schizobovine/uvdosimeter/hardware/uv-dosimeter-featherwing-mk-2.0.brd

## EAGLE design hardware/uv-dosimeter-featherwing-mk-2.0.brd (2016-05-01)

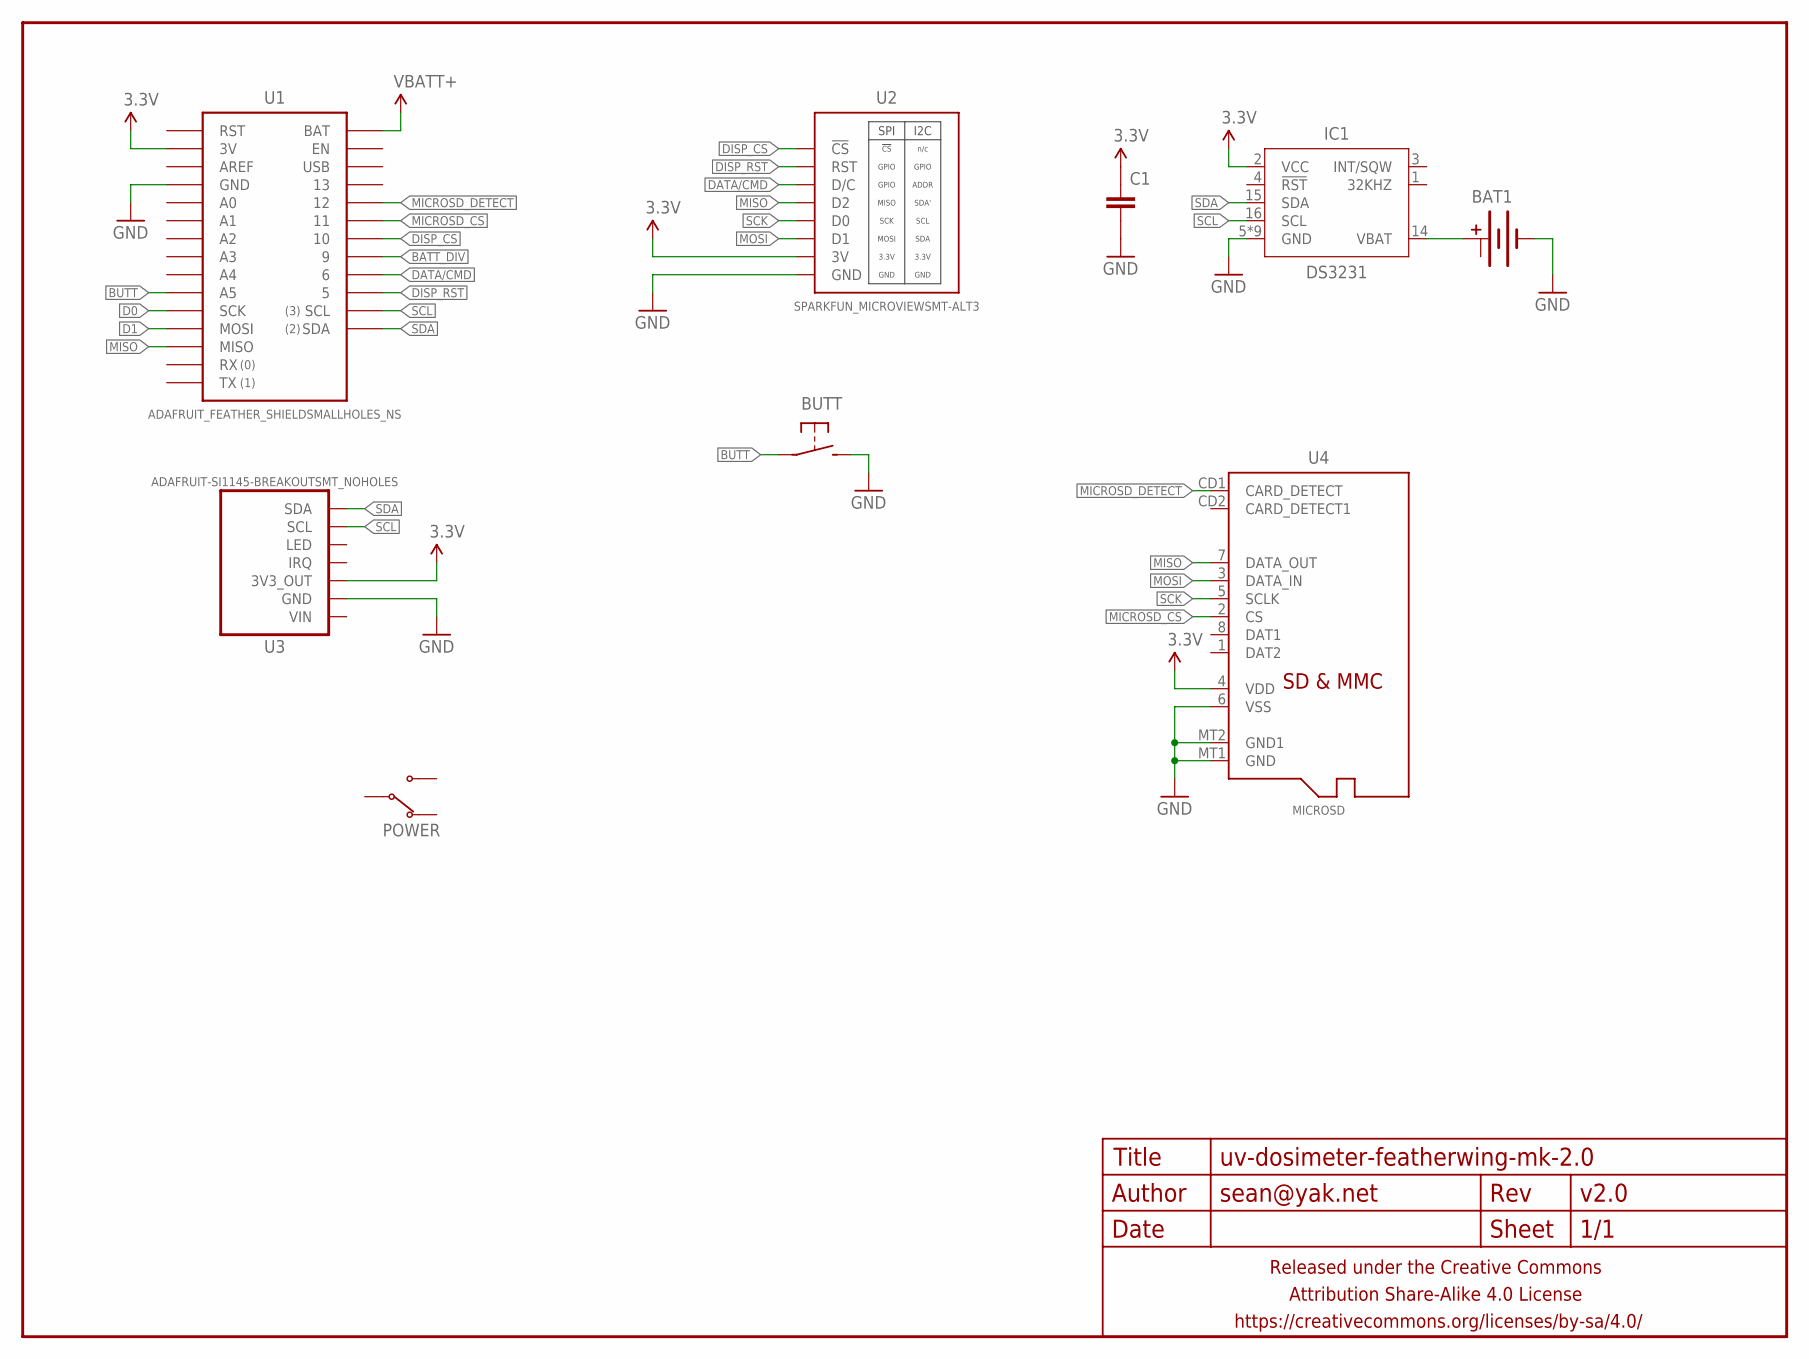
[picture p20: schematic uv-dosimeter-featherwing-mk-2.0.sch]

Parts:
BAT1: BATTERY-COINCR1225_SMD_SMALLER; BATTCON_12MM_SMD
BUTT: SPST-NO-TACT3MM-SMD; DTSM-3
C1: CAPACITOR-CERAMICC0603; C0603
FRAME1: FRAME-LETTERNO_PACKAGE; DUMMY
IC1: DS3231; SO16W
POWER: SWITCH-SPDTSMD-RA; SWITCH-SPDT-SMD-RA
U1: ADAFRUIT_FEATHER_SHIELDSMALLHOLES_NS; ADAFRUIT_FEATHER_SMALLHOLES_NS
U2: SPARKFUN_MICROVIEWSMT-ALT3; SPARKFUN-MICROVIEW-SMT-ALT3
U3: ADAFRUIT-SI1145-BREAKOUTSMT_NOHOLES; ADAFRUIT-SI1145-BREAKOUT-SMT-NOHOLES
U4: MICROSD

Connections:
3.3V: C1.1, IC1.2 (VCC), U1.3V, U2.3V, U3.3V3 (3V3_OUT)
BATT_DIV: U1.9
BUTT: BUTT.1, U1.A5
D0: U1.SCK
D1: U1.MOSI
DATA/CMD: U1.6, U2.D/C
DISP_CS: U1.10, U2.CS (!CS)
DISP_RST: U1.5, U2.RST
GND: BAT1.-, BUTT.2, C1.2, IC1.5 (GND), IC1.6 (GND), IC1.7 (GND), IC1.8 (GND), IC1.9 (GND), IC1.10 (GND), IC1.11 (GND), IC1.12 (GND), IC1.13 (GND), U1.GND@0 (GND), U1.GND@1 (GND), U2.GND, U3.GND, U4.6 (VSS), U4.MT1 (GND)
MICROSD_CS: U1.11, U4.2 (CS)
MICROSD_DETECT: U1.12, U4.CD1 (CARD_DETECT)
MISO: U1.MISO, U2.D2, U4.7 (DATA_OUT)
MOSI: U2.D1, U4.3 (DATA_IN)
unnamed: BAT1.+@1 (+), IC1.14 (VBAT)
SCK: U2.D0, U4.5 (SCLK)
SCL: IC1.16 (SCL), U1.SCL, U3.SCL
SDA: IC1.15 (SDA), U1.SDA, U3.SDA
VBATT+: U1.BAT
VDD: U4.4 (VDD)

Board: 2 copper layers, 12 parts (7 on the bottom side), 14 nets, no tracks yet.

Other parts of the board:
U$1: COW_SMALL
U$5: CC-BY-SA-4.0-NO-URL
