schizobovine/uvdosimeter/hardware/uv-dosimeter-featherwing-mk-1.3.brd

## EAGLE design hardware/uv-dosimeter-featherwing-mk-1.3.brd (2016-05-01)

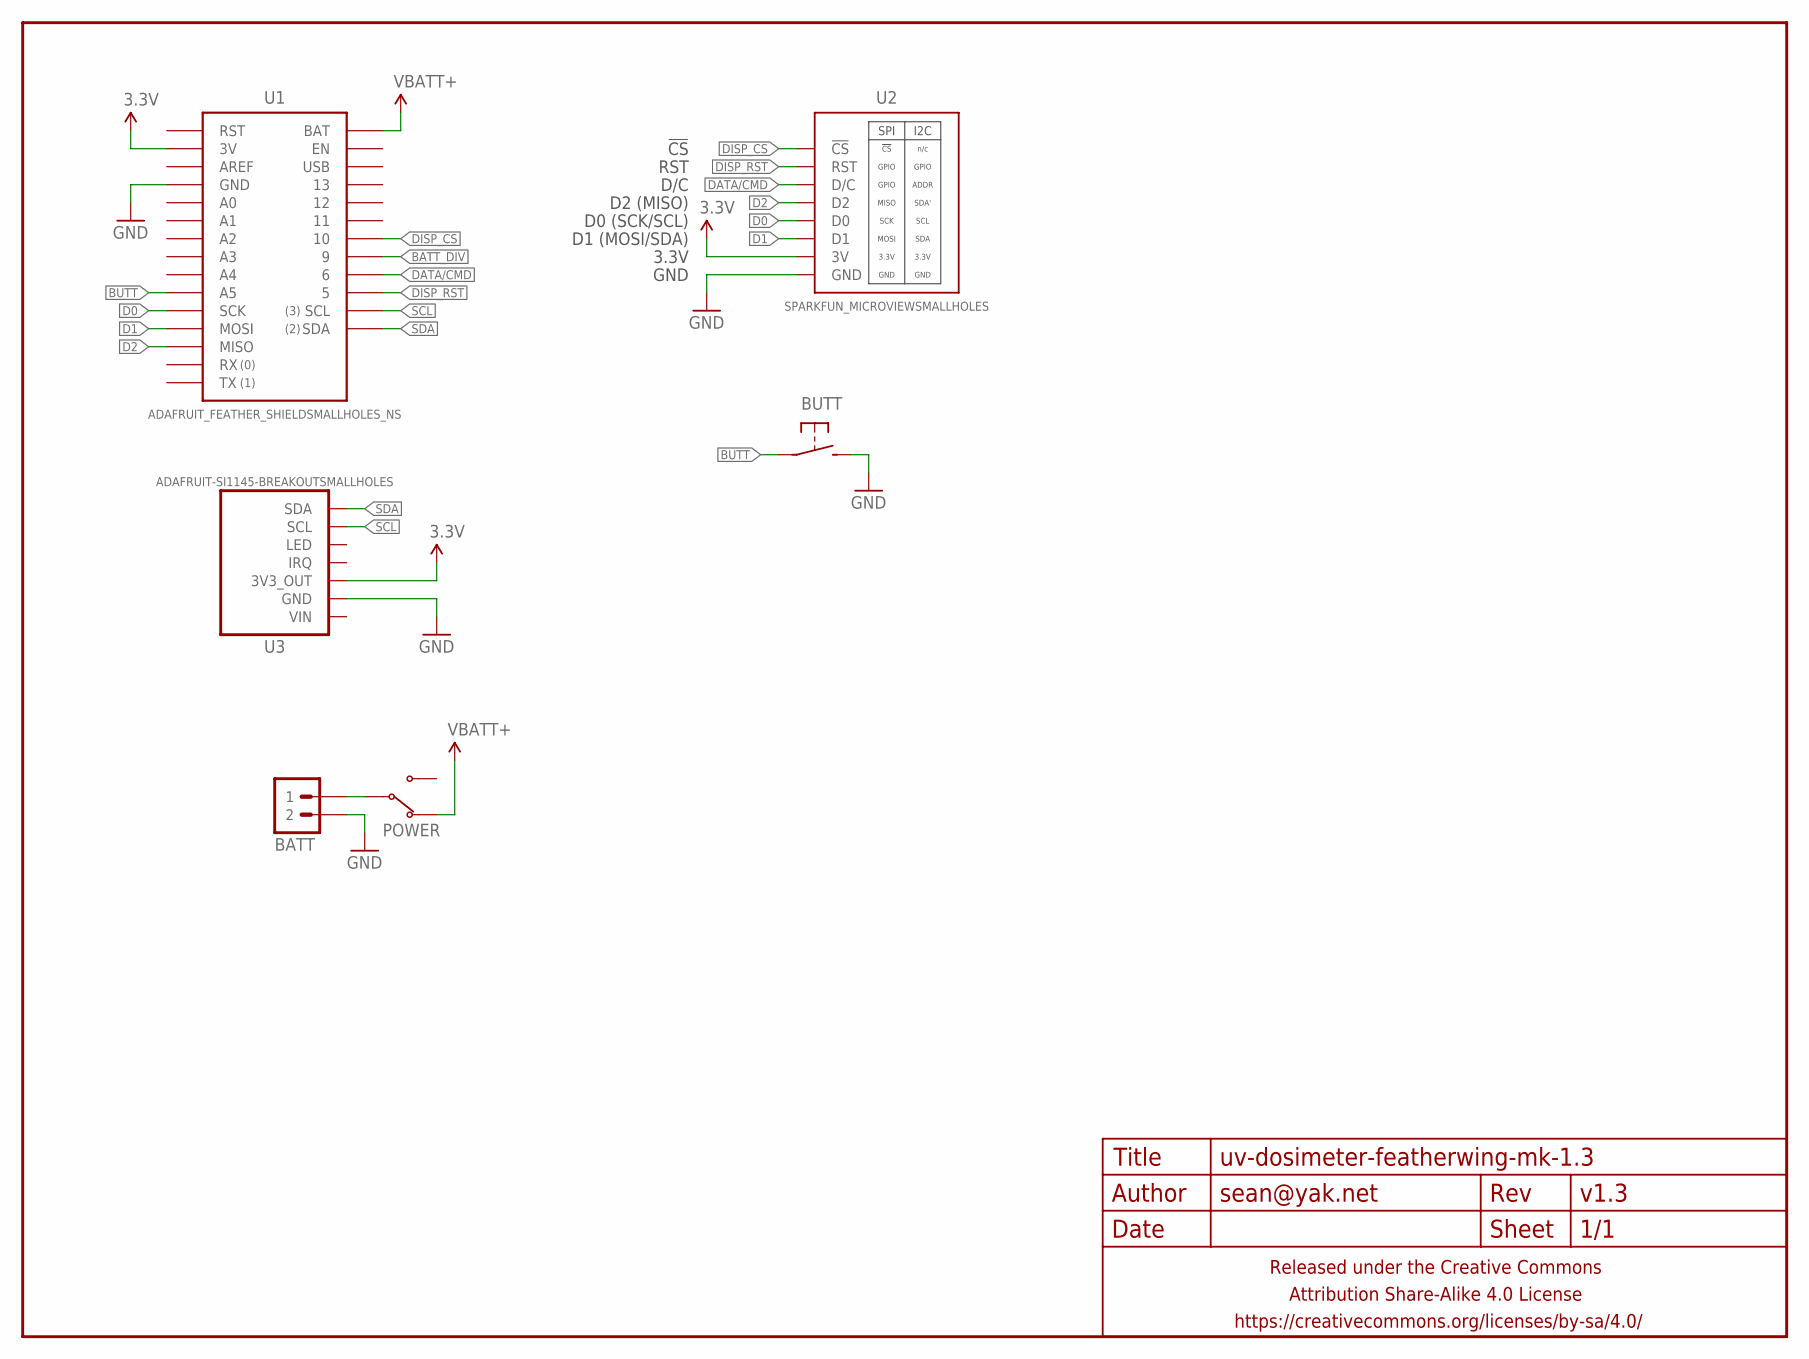
[picture p21: schematic uv-dosimeter-featherwing-mk-1.3.sch]

Parts:
BATT: M02JST-2MM-SMT; JST-2-SMD
BUTT: SPST-NO-TACT3MM-PTH-SMALL-PADS; DTS-3-SMALL-PADS
FRAME1: FRAME-LETTERNO_PACKAGE; DUMMY
POWER: SWITCH-SPDTPTH-VERT-2.54MM; SWITCH-SPDT
U1: ADAFRUIT_FEATHER_SHIELDSMALLHOLES_NS; ADAFRUIT_FEATHER_SMALLHOLES_NS
U2: SPARKFUN_MICROVIEWSMALLHOLES; SPARKFUN-MICROVIEW-SMALLHOLES
U3: ADAFRUIT-SI1145-BREAKOUTSMALLHOLES; ADAFRUIT-SI1145-BREAKOUT-LESSSILK-SMALLHOLES

Connections:
3.3V: U1.3V, U2.3V, U3.3V3_OUT
BATT_DIV: U1.9
BUTT: BUTT.1, U1.A5
D0: U1.SCK, U2.D0
D1: U1.MOSI, U2.D1
D2: U1.MISO, U2.D2
DATA/CMD: U1.6, U2.D/C
DISP_CS: U1.10, U2.CS (!CS)
DISP_RST: U1.5, U2.RST
GND: BATT.1 (2), BUTT.2, U1.GND@0 (GND), U1.GND@1 (GND), U2.GND, U3.GND
unnamed: BATT.2 (1), POWER.2 (COM)
SCL: U1.SCL, U3.SCL
SDA: U1.SDA, U3.SDA
VBATT+: POWER.1 (NC), U1.BAT

Notes on the sheet:
GND
3.3V
D1 (MOSI/SDA)
D0 (SCK/SCL)
D2 (MISO)
D/C
RST
!CS

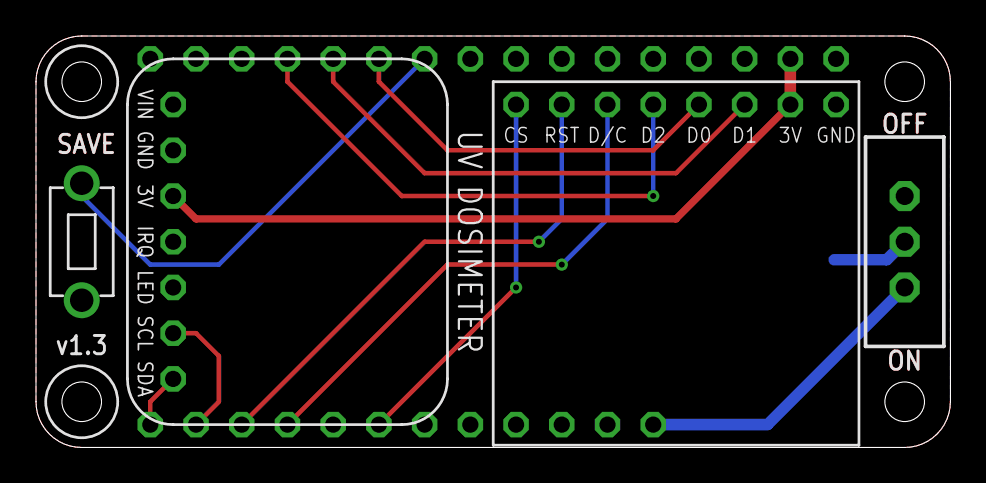
[picture p22: board uv-dosimeter-featherwing-mk-1.3.brd from above]

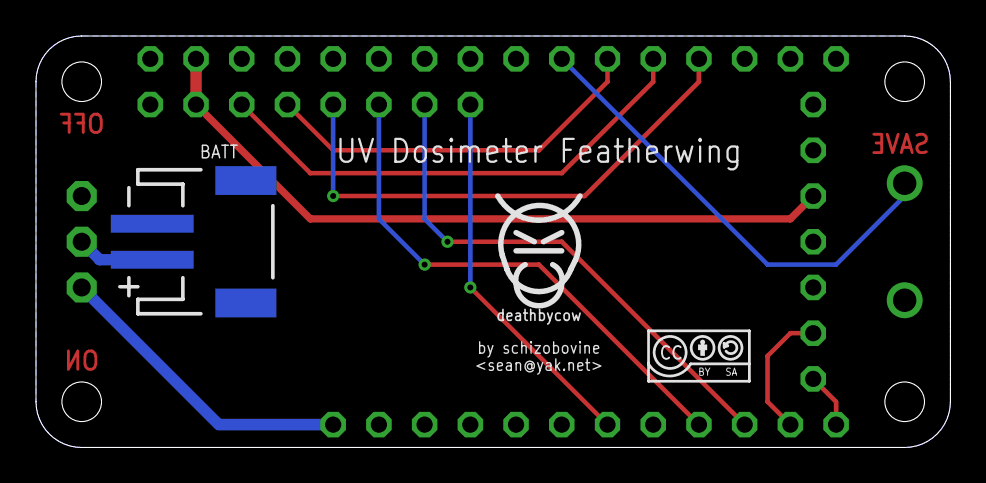
[picture p23: board uv-dosimeter-featherwing-mk-1.3.brd from below]

Board: 2 copper layers, 50.8 x 22.9 mm, 9 parts (4 on the bottom side), 13 nets.

Other parts of the board:
U$1: COW_SMALL
U$5: CC-BY-SA-4.0-NO-URL
