schizobovine/uvdosimeter/hardware/uv-dosimeter-featherwing-mk-1.0.brd

## EAGLE design hardware/uv-dosimeter-featherwing-mk-1.0.brd (2016-04-16)

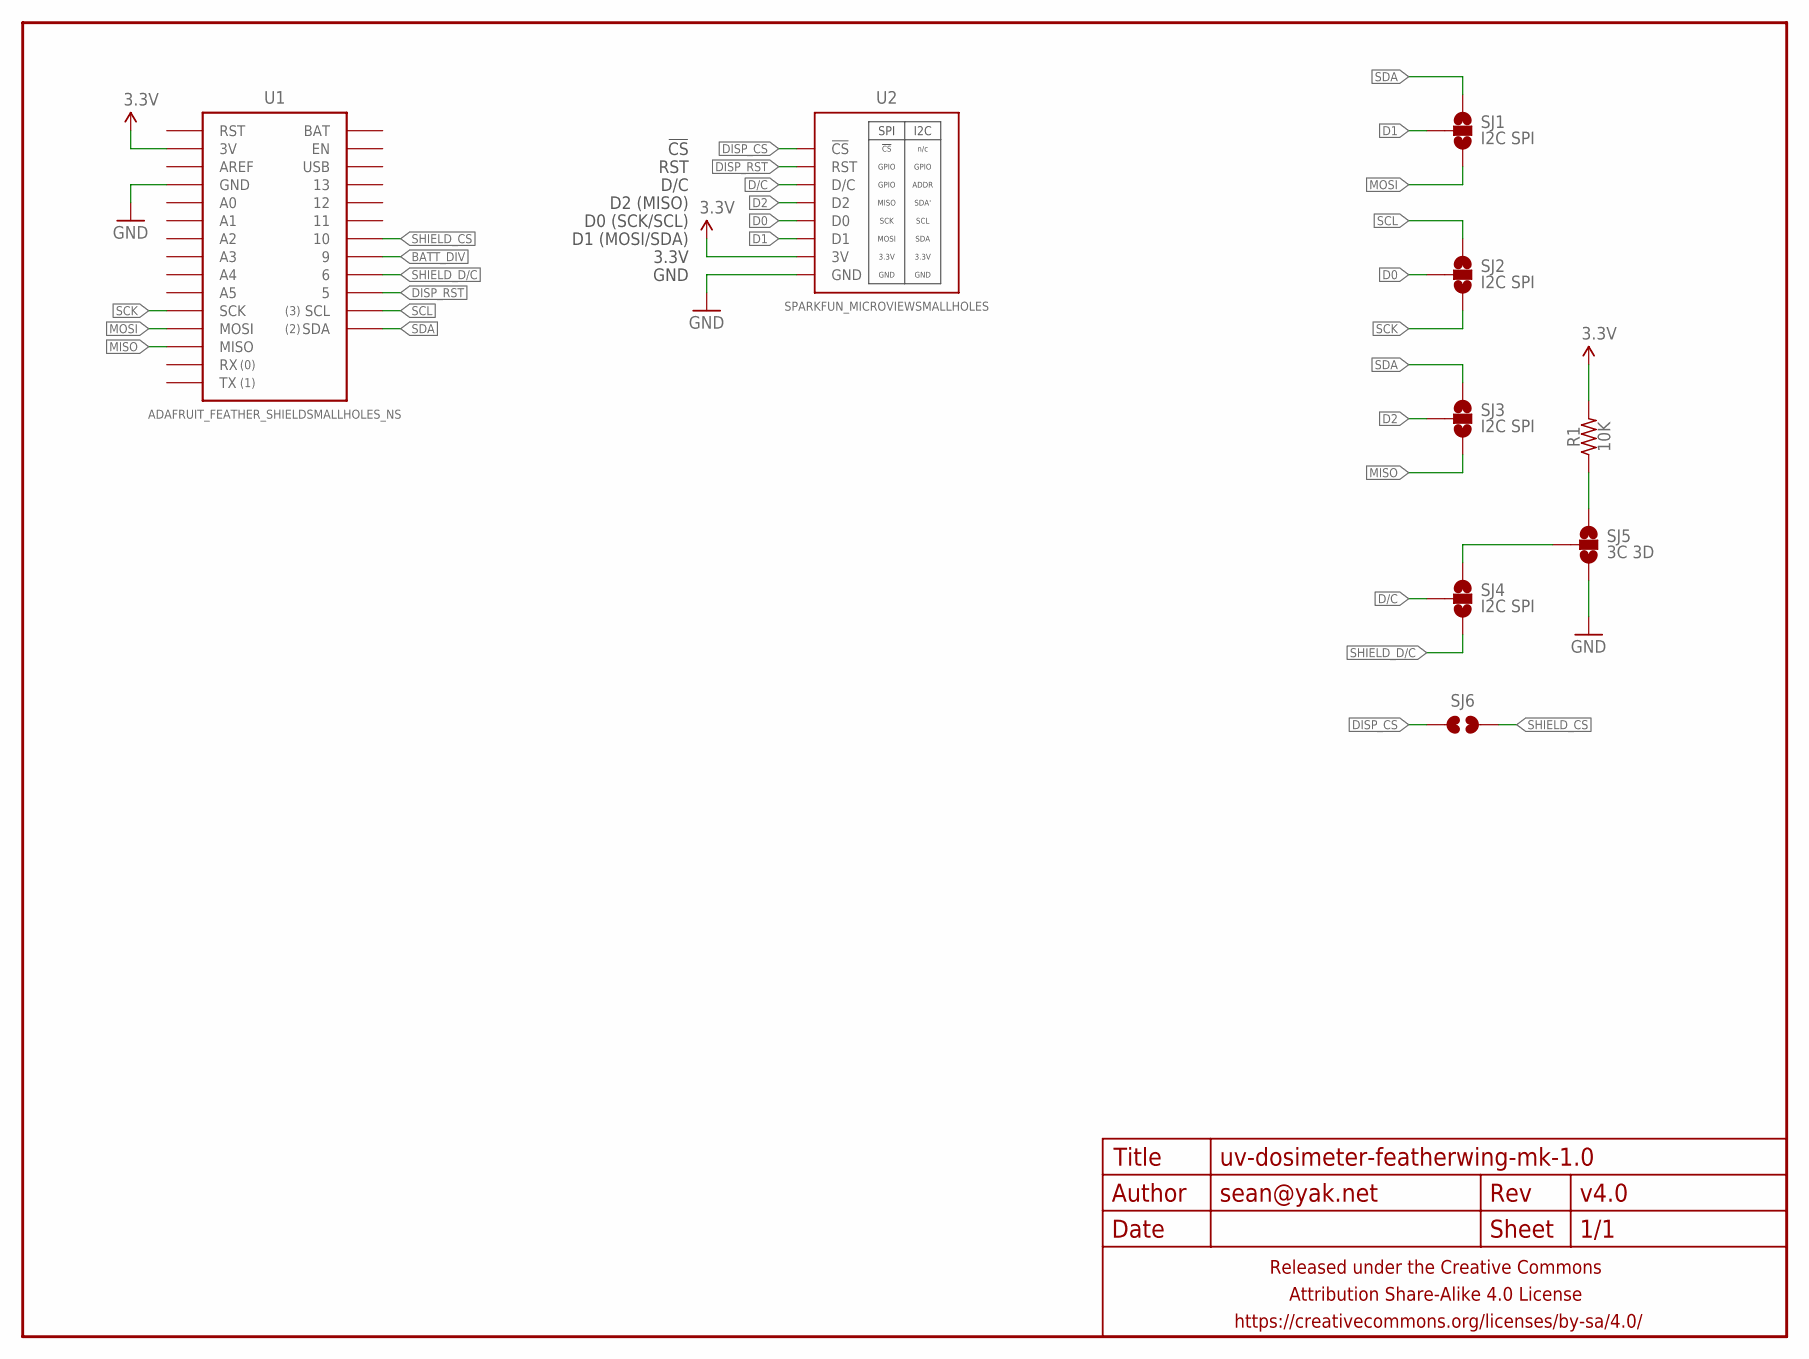
[picture p24: schematic uv-dosimeter-featherwing-mk-1.0.sch]

Parts:
FRAME1: FRAME-LETTERNO_PACKAGE; DUMMY
R1: 10K; R0603
SJ1, SJ2, SJ3, SJ4: I2C SPI; PAD-JUMPER-3-NO_YES_SILK_FULL_BOX
SJ5: 3C 3D; PAD-JUMPER-3-NO_YES_SILK_FULL_BOX
SJ6: JUMPER-PAD-2-NOYES_SILK; PAD-JUMPER-2-NO_YES_SILK
U1: ADAFRUIT_FEATHER_SHIELDSMALLHOLES_NS; ADAFRUIT_FEATHER_SMALLHOLES_NS
U2: SPARKFUN_MICROVIEWSMALLHOLES; SPARKFUN-MICROVIEW-SMALLHOLES

Connections:
3.3V: R1.2, U1.3V, U2.3V
BATT_DIV: U1.9
D0: SJ2.2, U2.D0
D1: U2.D1
D2: U2.D2
D/C: U2.D/C
DISP_CS: SJ6.1, U2.CS (!CS)
DISP_RST: U1.5, U2.RST
GND: SJ5.3, U1.GND@0 (GND), U1.GND@1 (GND), U2.GND
MISO: SJ3.3, U1.MISO
MOSI: SJ1.3, U1.MOSI
unnamed: R1.1, SJ5.1
unnamed: SJ4.1, SJ5.2
SCK: SJ2.3, U1.SCK
SCL: SJ2.1, U1.SCL
SDA: SJ1.1, U1.SDA
SHIELD_CS: SJ6.2, U1.10
SHIELD_D/C: SJ4.3, U1.6

Notes on the sheet:
GND
3.3V
D1 (MOSI/SDA)
D0 (SCK/SCL)
D2 (MISO)
D/C
RST
!CS

Board: 2 copper layers, 12 parts (3 on the bottom side), 14 nets, no tracks yet.

Other parts of the board:
U$1: COW_SMALL
U$3: OSHWLOGO_TINY_SILKONLY
