schizobovine/uvdosimeter/hardware/tinyduino-breakout-mk-4.0.brd

## EAGLE design hardware/tinyduino-breakout-mk-4.0.brd (2016-03-02)

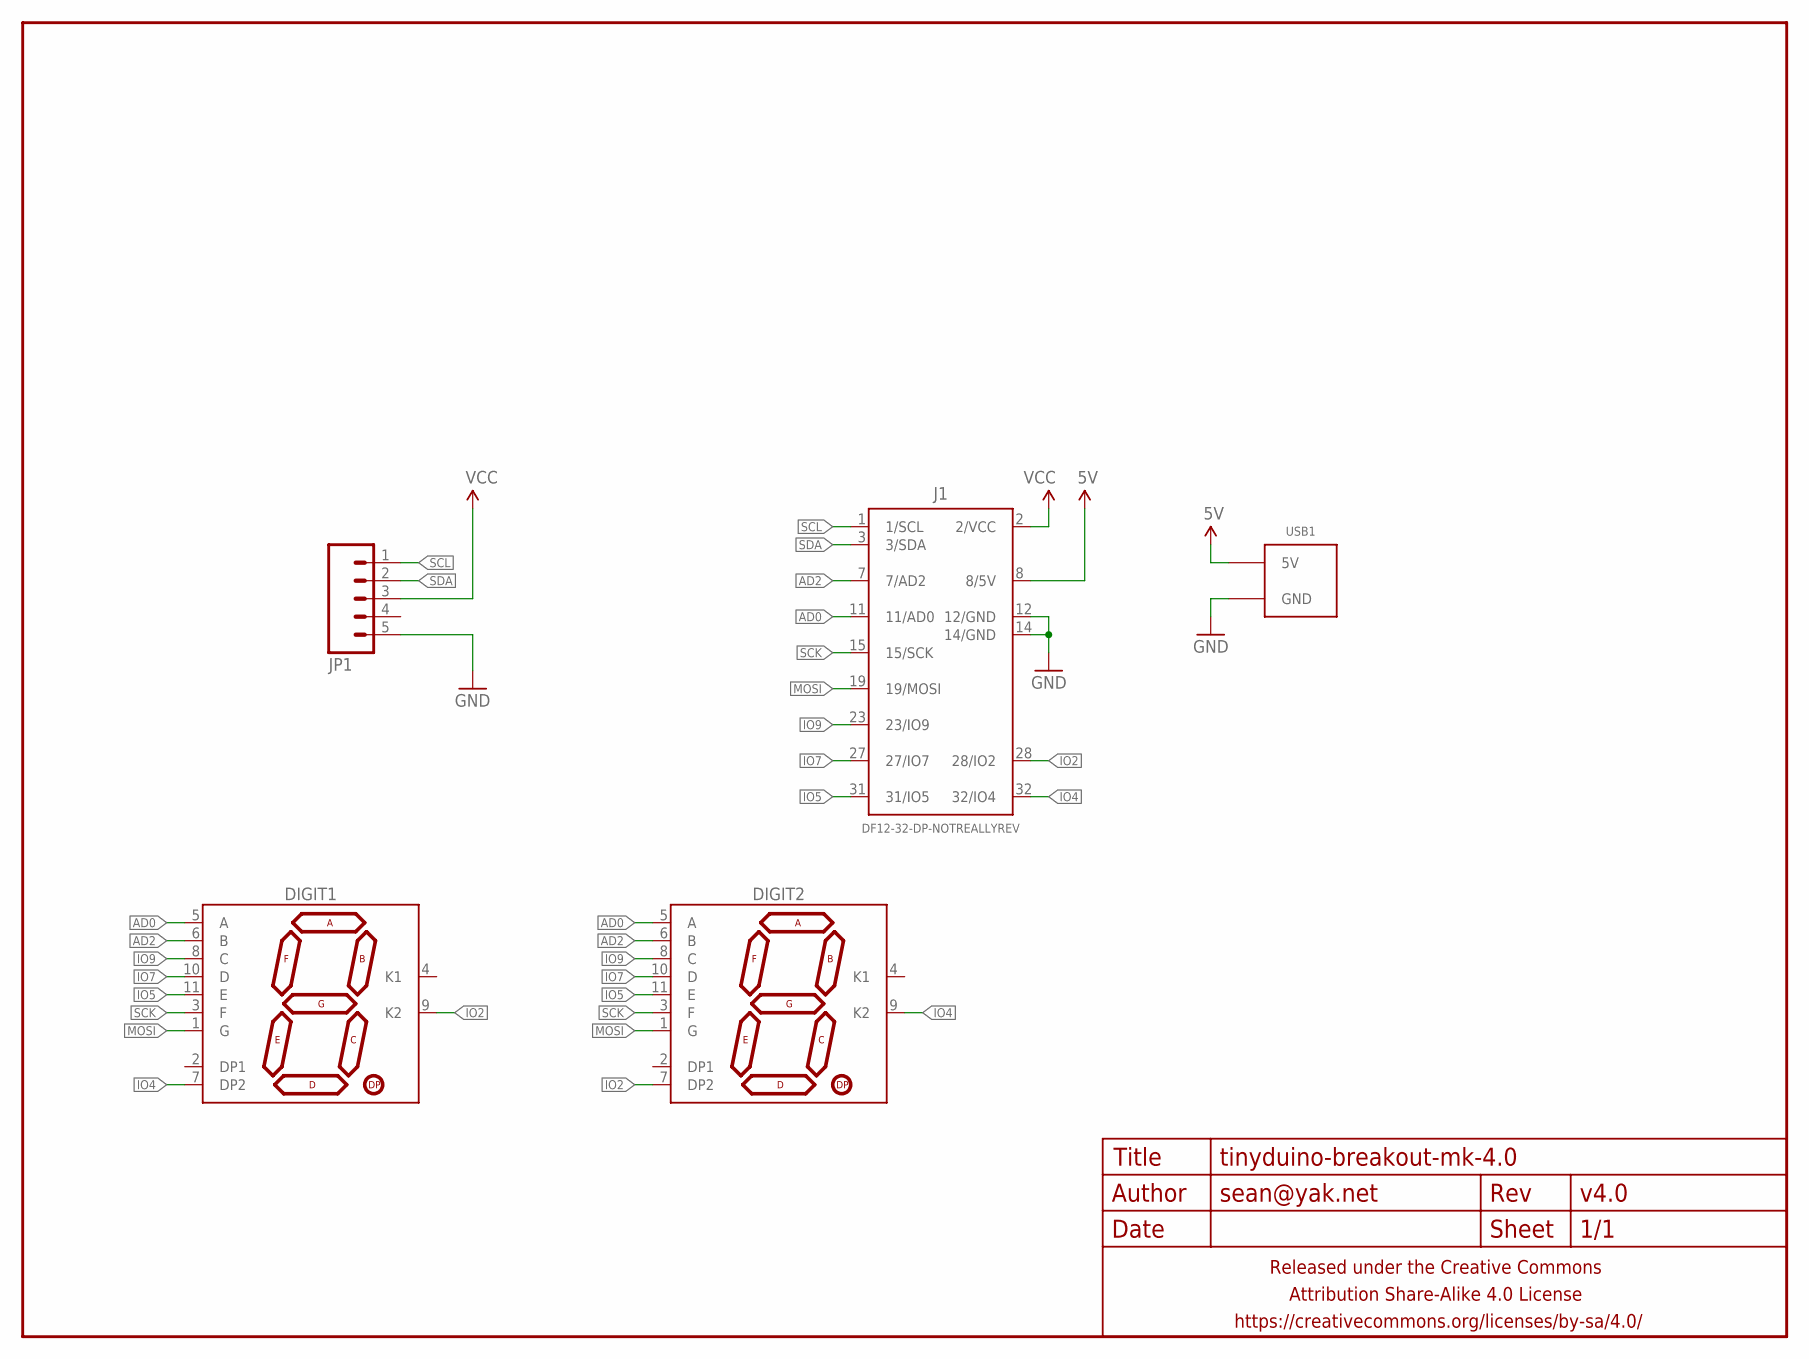
[picture p25: schematic tinyduino-breakout-mk-4.0.sch]

Parts:
DIGIT1, DIGIT2: 7SEG_1DIG_2DP7MM_CC_SMT; 7SEG_1DIG_7MM_SMT
FRAME1: FRAME-LETTERNO_PACKAGE; DUMMY
J1: DF12-32-DP-NOTREALLYREV; DF12-32-DP-I2C+EXTRA-REV
JP1: M05PTH-CENTERED; 1X05_PTH_CENTERED
USB1: USB_AB_PWRONLY; FCI-10103594-USB-MICRO-B-PWRONLY

Connections:
5V: J1.8 (8/5V), USB1.1 (5V)
AD0: DIGIT1.5 (A), DIGIT2.5 (A), J1.11 (11/AD0)
AD2: DIGIT1.6 (B), DIGIT2.6 (B), J1.7 (7/AD2)
GND: J1.12 (12/GND), J1.14 (14/GND), JP1.5, USB1.5 (GND), USB1.SHIELD@1 (GND), USB1.SHIELD@2 (GND), USB1.SHIELD@3 (GND), USB1.SHIELD@4 (GND)
IO2: DIGIT1.9 (K2), DIGIT2.7 (DP2), J1.28 (28/IO2)
IO4: DIGIT1.7 (DP2), DIGIT2.9 (K2), J1.32 (32/IO4)
IO5: DIGIT1.11 (E), DIGIT2.11 (E), J1.31 (31/IO5)
IO7: DIGIT1.10 (D), DIGIT2.10 (D), J1.27 (27/IO7)
IO9: DIGIT1.8 (C), DIGIT2.8 (C), J1.23 (23/IO9)
MOSI: DIGIT1.1 (G), DIGIT2.1 (G), J1.19 (19/MOSI)
SCK: DIGIT1.3 (F), DIGIT2.3 (F), J1.15 (15/SCK)
SCL: J1.1 (1/SCL), JP1.1
SDA: J1.3 (3/SDA), JP1.2
VCC: J1.2 (2/VCC), JP1.3

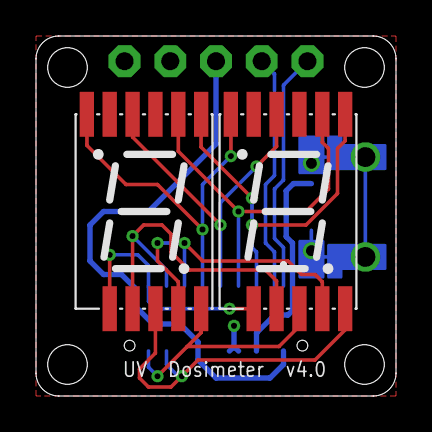
[picture p26: board tinyduino-breakout-mk-4.0.brd from above]

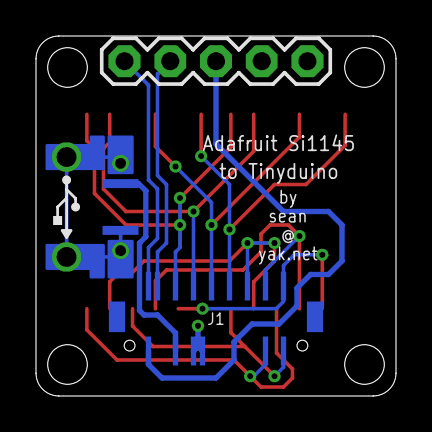
[picture p27: board tinyduino-breakout-mk-4.0.brd from below]

Board: 2 copper layers, 20.0 x 20.0 mm, 6 parts (2 on the bottom side), 14 nets.
