schizobovine/uvdosimeter/hardware/tinyduino-breakout-mk-3.0.brd

## EAGLE design hardware/tinyduino-breakout-mk-3.0.brd (2016-02-28)

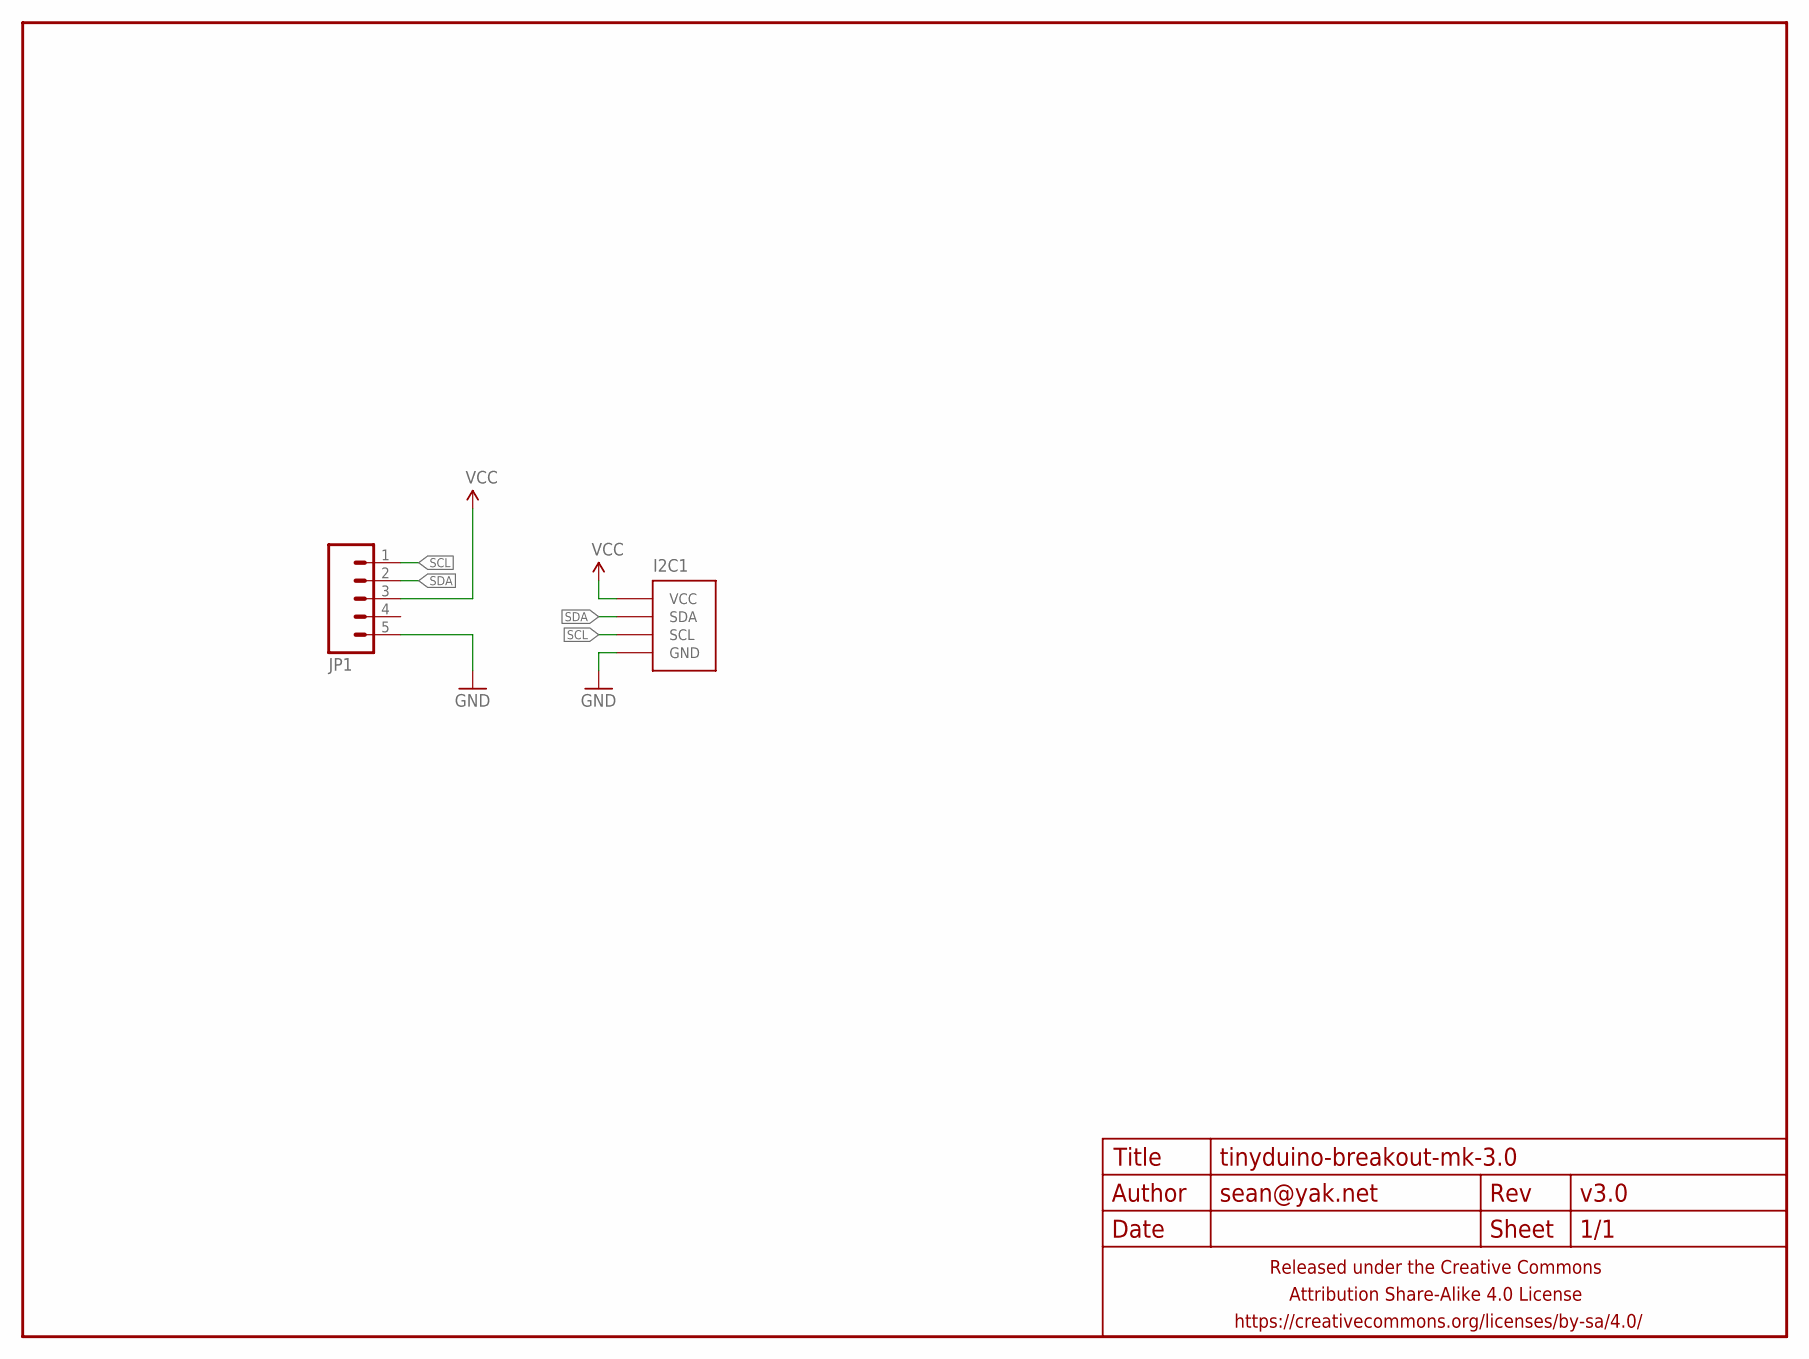
[picture p28: schematic tinyduino-breakout-mk-3.0.sch]

Parts:
FRAME1: FRAME-LETTERNO_PACKAGE; DUMMY
I2C1: M04-I2CTINYDUINO-CONNECTOR-REV; DF12-32-DP-I2CONLY-REV
JP1: M05SMD-SHORT; 1X05-SMD-SHORT

Connections:
GND: I2C1.12 (GND), I2C1.14 (GND), JP1.5
SCL: I2C1.1 (SCL), JP1.1
SDA: I2C1.3 (SDA), JP1.2
VCC: I2C1.2 (VCC), JP1.3

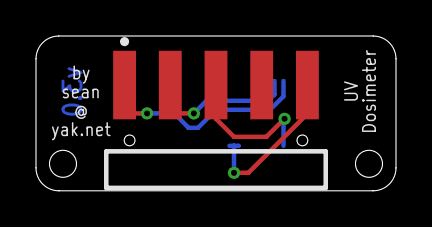
[picture p29: board tinyduino-breakout-mk-3.0.brd from above]

Board: 2 copper layers, 20.0 x 8.6 mm, 3 parts (0 on the bottom side), 4 nets.
