schizobovine/uvdosimeter/hardware/tinyduino-breakout-mk-2.1.brd

## EAGLE design hardware/tinyduino-breakout-mk-2.1.brd (2016-02-28)

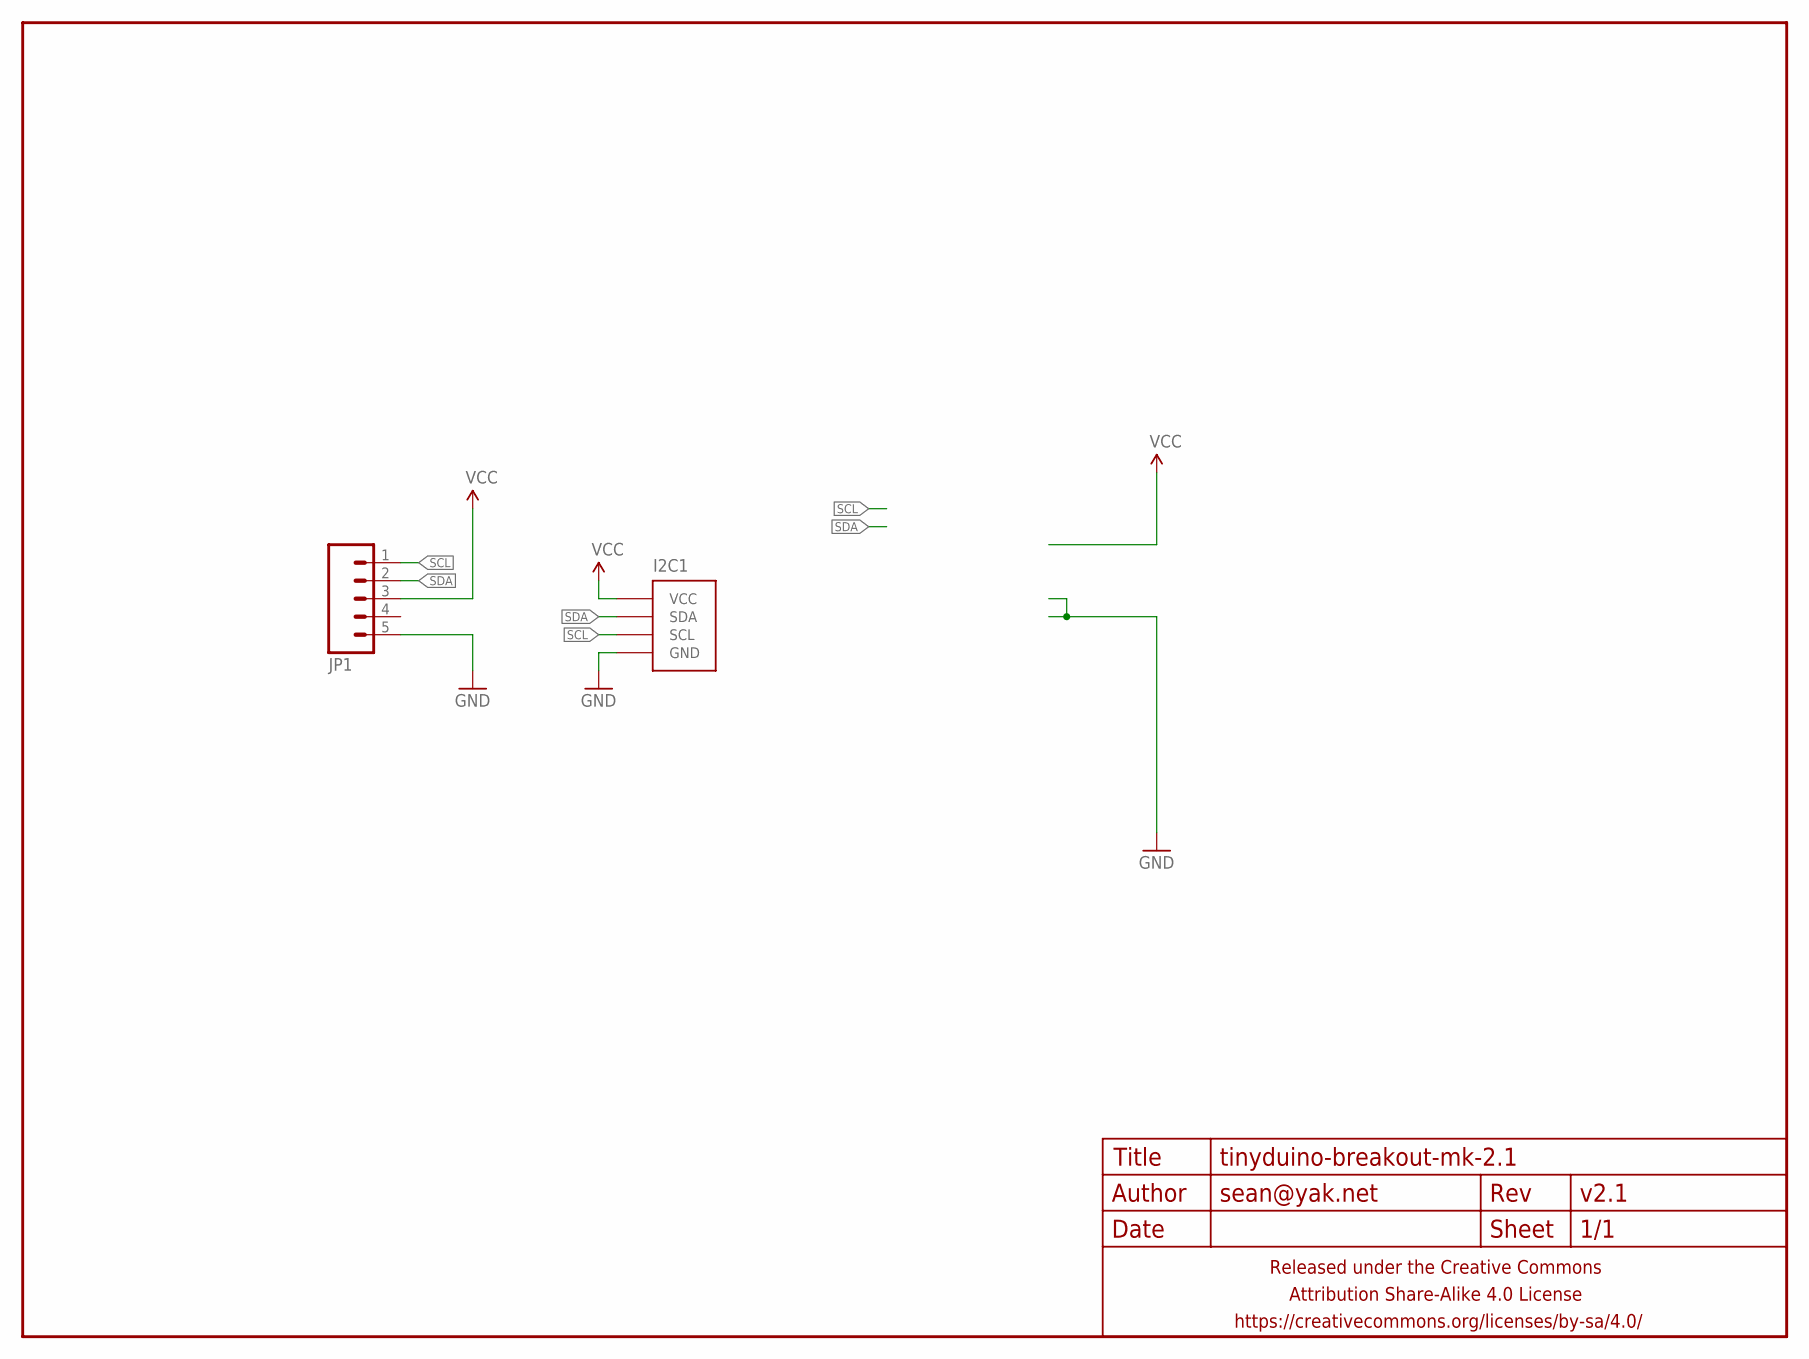
[picture p30: schematic tinyduino-breakout-mk-2.1.sch]

Parts:
FRAME1: FRAME-LETTERNO_PACKAGE; DUMMY
I2C1: M04-I2CTINDUINO-CONNECTOR-REV; DF12-32-DP-I2CONLY
JP1: M05SMD-SHORT; 1X05-SMD-SHORT

Connections:
GND: I2C1.11 (GND), I2C1.13 (GND), JP1.5
SCL: JP1.1
SDA: JP1.2
VCC: I2C1.5 (VCC), JP1.3

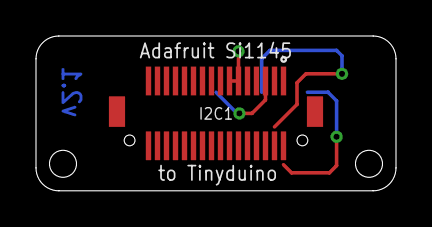
[picture p31: board tinyduino-breakout-mk-2.1.brd from above]

Board: 2 copper layers, 20.0 x 8.6 mm, 3 parts (1 on the bottom side), 2 nets.
