schizobovine/uvdosimeter/hardware/tinyduino-breakout-mk-2.0.brd

## EAGLE design hardware/tinyduino-breakout-mk-2.0.brd (2016-01-18)

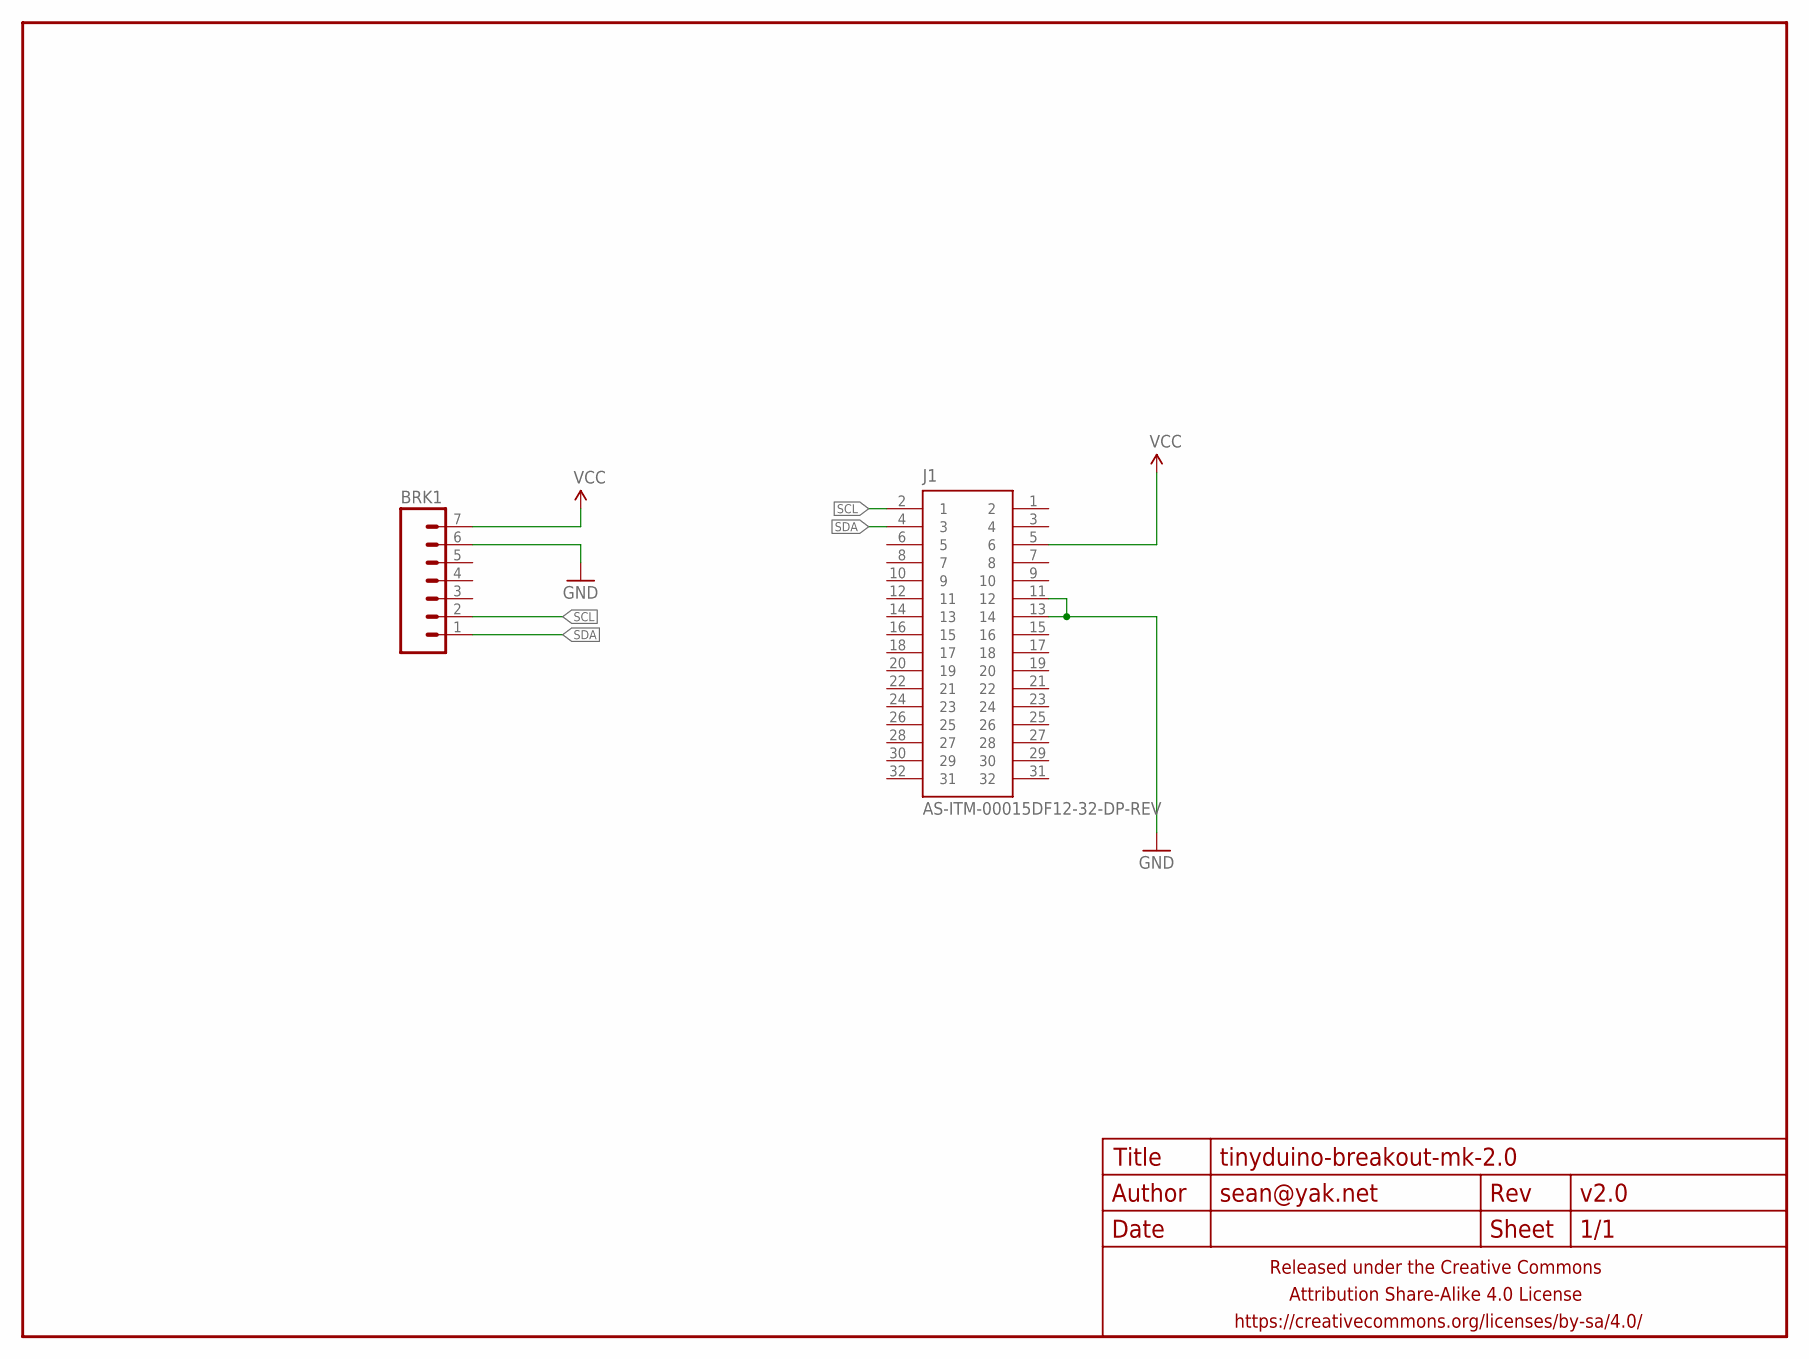
[picture p32: schematic tinyduino-breakout-mk-2.0.sch]

Parts:
BRK1: ADAFRUIT-SI1145-BREAKOUTSMD-RA; 1X07-SMD-SHORT
FRAME1: FRAME-LETTERNO_PACKAGE; DUMMY
J1: AS-ITM-00015DF12-32-DP-REV; DF12-32-DP

Connections:
GND: BRK1.6 (GND), J1.11 (12), J1.13 (14)
SCL: BRK1.2 (SCL), J1.2 (1)
SDA: BRK1.1 (SDA), J1.4 (3)
VCC: BRK1.7 (VIN), J1.5 (6)

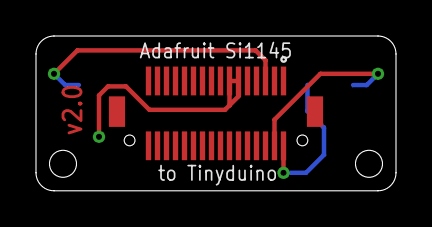
[picture p33: board tinyduino-breakout-mk-2.0.brd from above]

Board: 2 copper layers, 20.0 x 8.6 mm, 3 parts (1 on the bottom side), 4 nets.
