schizobovine/uvdosimeter/hardware/tinyduino-breakout-mk-1.0.brd

## EAGLE design hardware/tinyduino-breakout-mk-1.0.brd (2016-01-18)

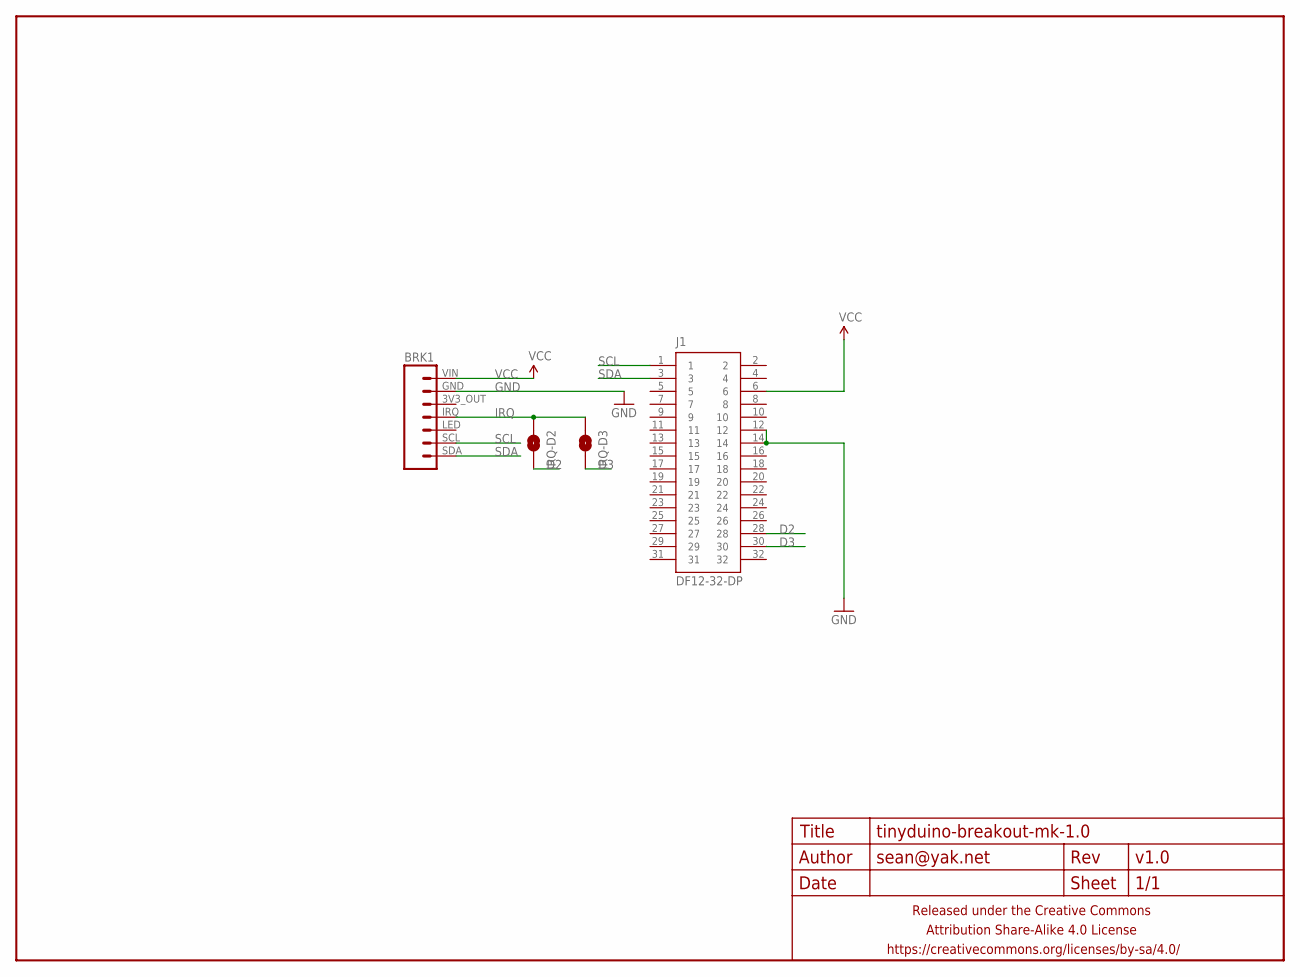
[picture p34: schematic tinyduino-breakout-mk-1.0.sch]

Parts:
BRK1: ADAFRUIT-SI1145-BREAKOUT
FRAME1: FRAME-LETTERNO_PACKAGE; DUMMY
IRQ-D2, IRQ-D3: JUMPER-PAD-2-NOYES_SILK; PAD-JUMPER-2-NO_YES_SILK
J1: DF12-32-DP

Connections:
D2: IRQ-D2.2, J1.28
D3: IRQ-D3.2, J1.30
GND: BRK1.GND, J1.12, J1.14
IRQ: BRK1.IRQ, IRQ-D2.1, IRQ-D3.1
SCL: BRK1.SCL, J1.1
SDA: BRK1.SDA, J1.3
VCC: BRK1.VIN, J1.6

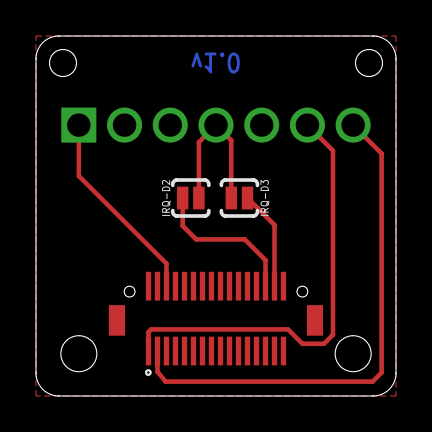
[picture p35: board tinyduino-breakout-mk-1.0.brd from above]

Board: 2 copper layers, 20.0 x 20.0 mm, 5 parts (1 on the bottom side), 7 nets.
