schizobovine/uvdosimeter/hardware/feather-power-switch-mk-2.0.brd

## EAGLE design hardware/feather-power-switch-mk-2.0.brd (2016-01-18)

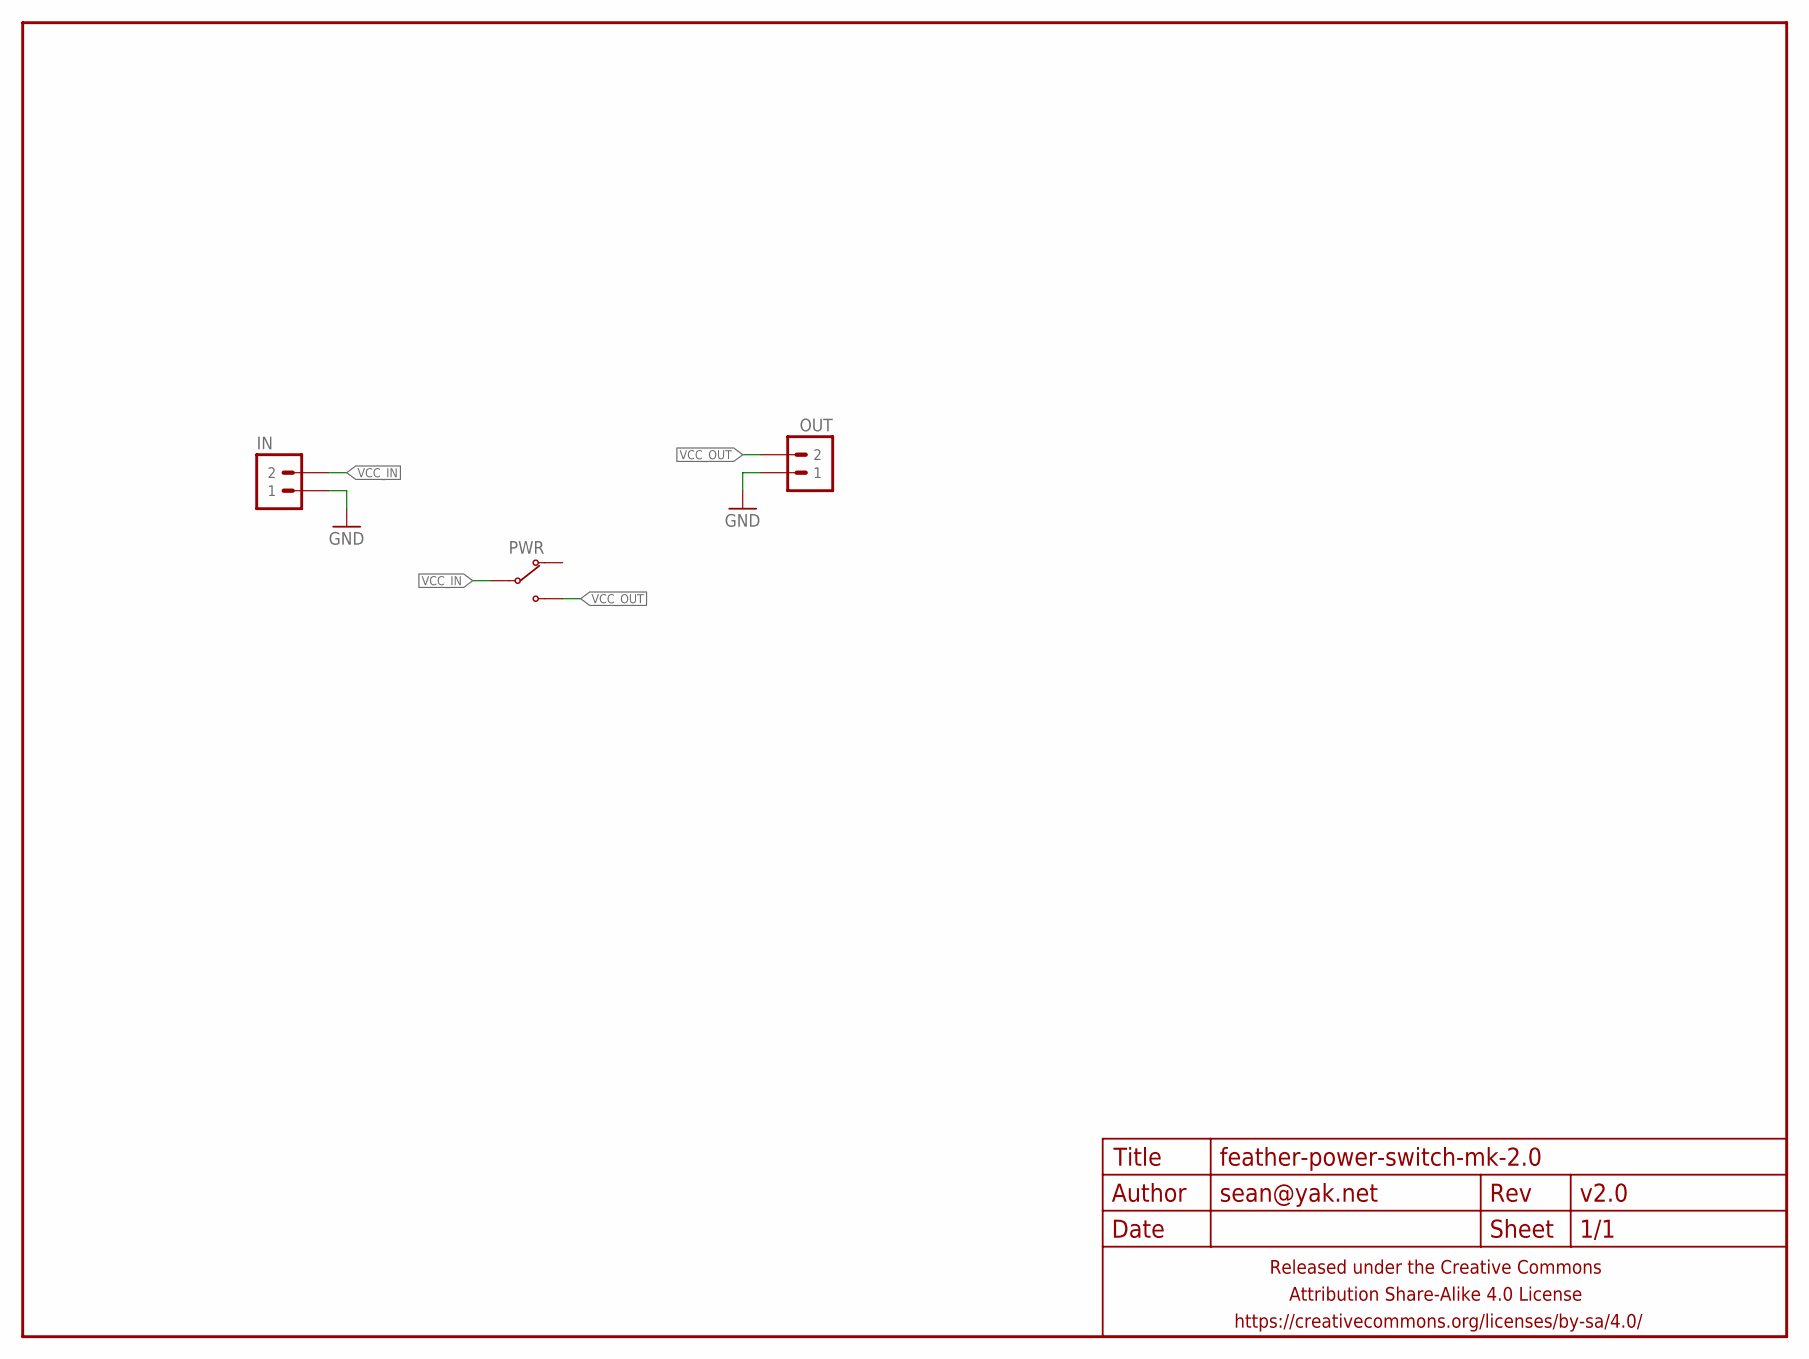
[picture p36: schematic feather-power-switch-mk-2.0.sch]

Parts:
FRAME1: FRAME-LETTERNO_PACKAGE; DUMMY
IN: M02PTH-CENTERED-R+; 1X02-CENTER-R+
OUT: M02PTH-CENTERED-R+; 1X02-CENTER-R+
PWR: SWITCH-SPDTSMD-RA; SWITCH-SPDT-SMD-RA

Connections:
GND: IN.1, OUT.1
VCC_IN: IN.2, PWR.2 (COM)
VCC_OUT: OUT.2, PWR.1 (NO)

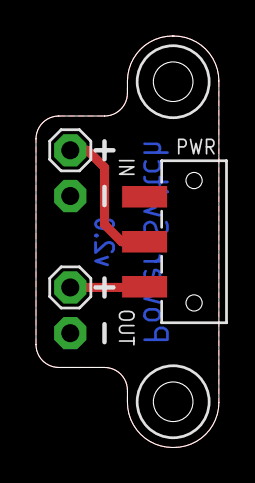
[picture p37: board feather-power-switch-mk-2.0.brd from above]

Board: 2 copper layers, 10.2 x 22.9 mm, 4 parts (0 on the bottom side), 3 nets.
