schizobovine/uvdosimeter/hardware/feather-power-switch-mk-1.0.brd

## EAGLE design hardware/feather-power-switch-mk-1.0.brd (2016-01-18)

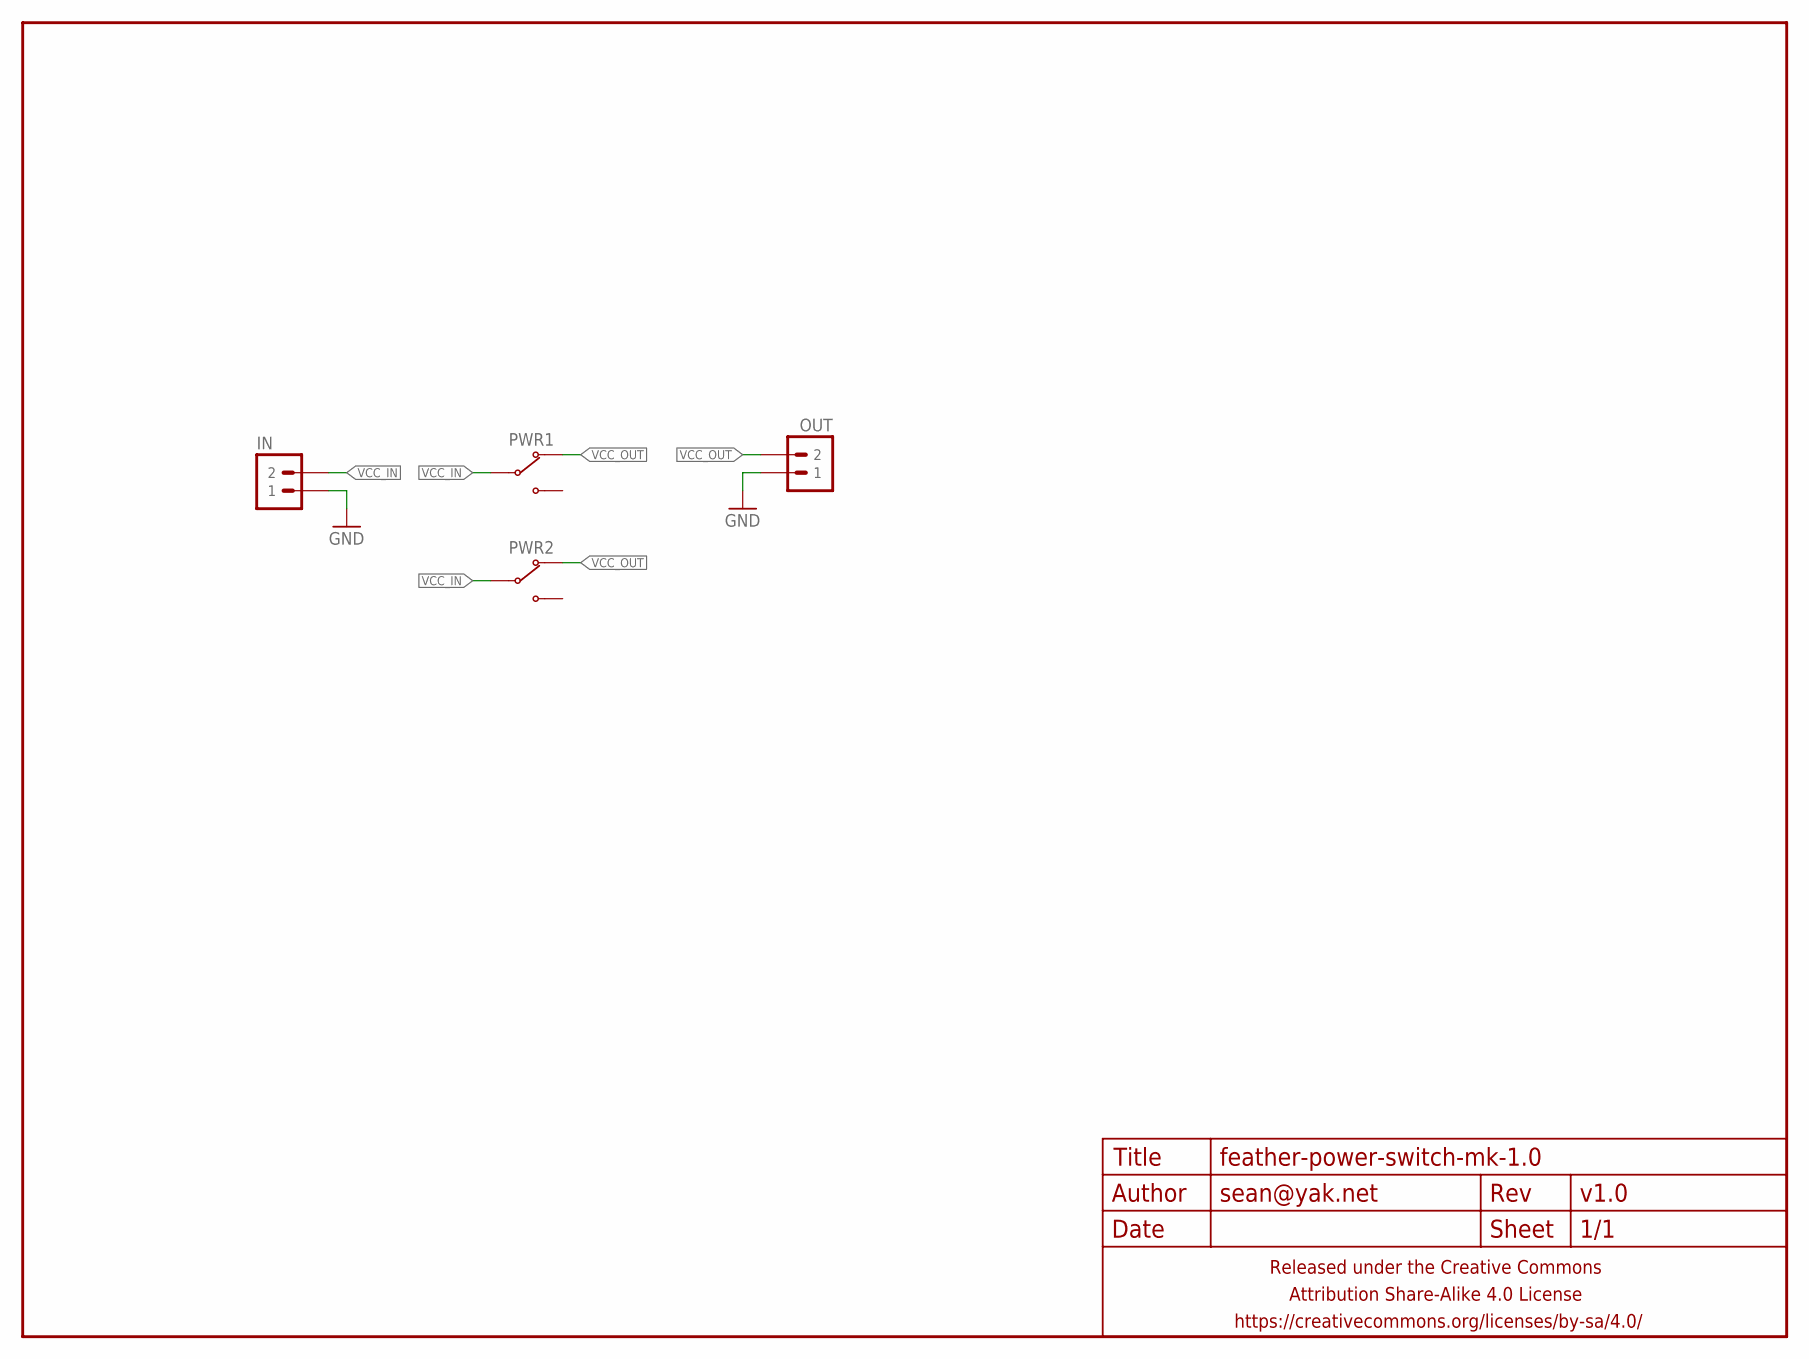
[picture p38: schematic feather-power-switch-mk-1.0.sch]

Parts:
FRAME1: FRAME-LETTERNO_PACKAGE; DUMMY
IN: M02JST-PTH-RA-R+; JST-2-PH-RA-PTH-R+
OUT: M02PTH-CENTERED-R+; 1X02-CENTER-R+
PWR1, PWR2: SWITCH-SPDTPCM12SMTR; SWITCH-SPDT-SMD-RA-PCM12SMTR

Connections:
GND: IN.1, OUT.1
VCC_IN: IN.2, PWR1.2 (COM), PWR2.2 (COM)
VCC_OUT: OUT.2, PWR1.1 (NC), PWR2.1 (NC)

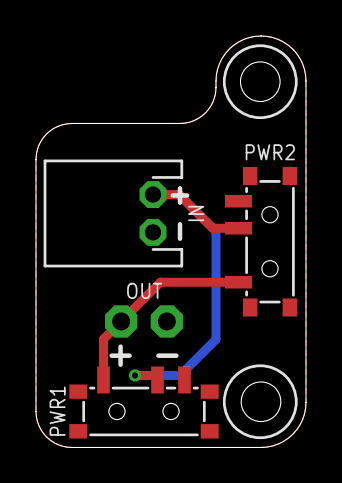
[picture p39: board feather-power-switch-mk-1.0.brd from above]

Board: 2 copper layers, 15.0 x 22.9 mm, 5 parts (1 on the bottom side), 3 nets.
