schizobovine/uvdosimeter/hardware/ultra-violet-tooth-sensor-mk-3.3.brd

## EAGLE design hardware/ultra-violet-tooth-sensor-mk-3.3.brd (2015-06-22)

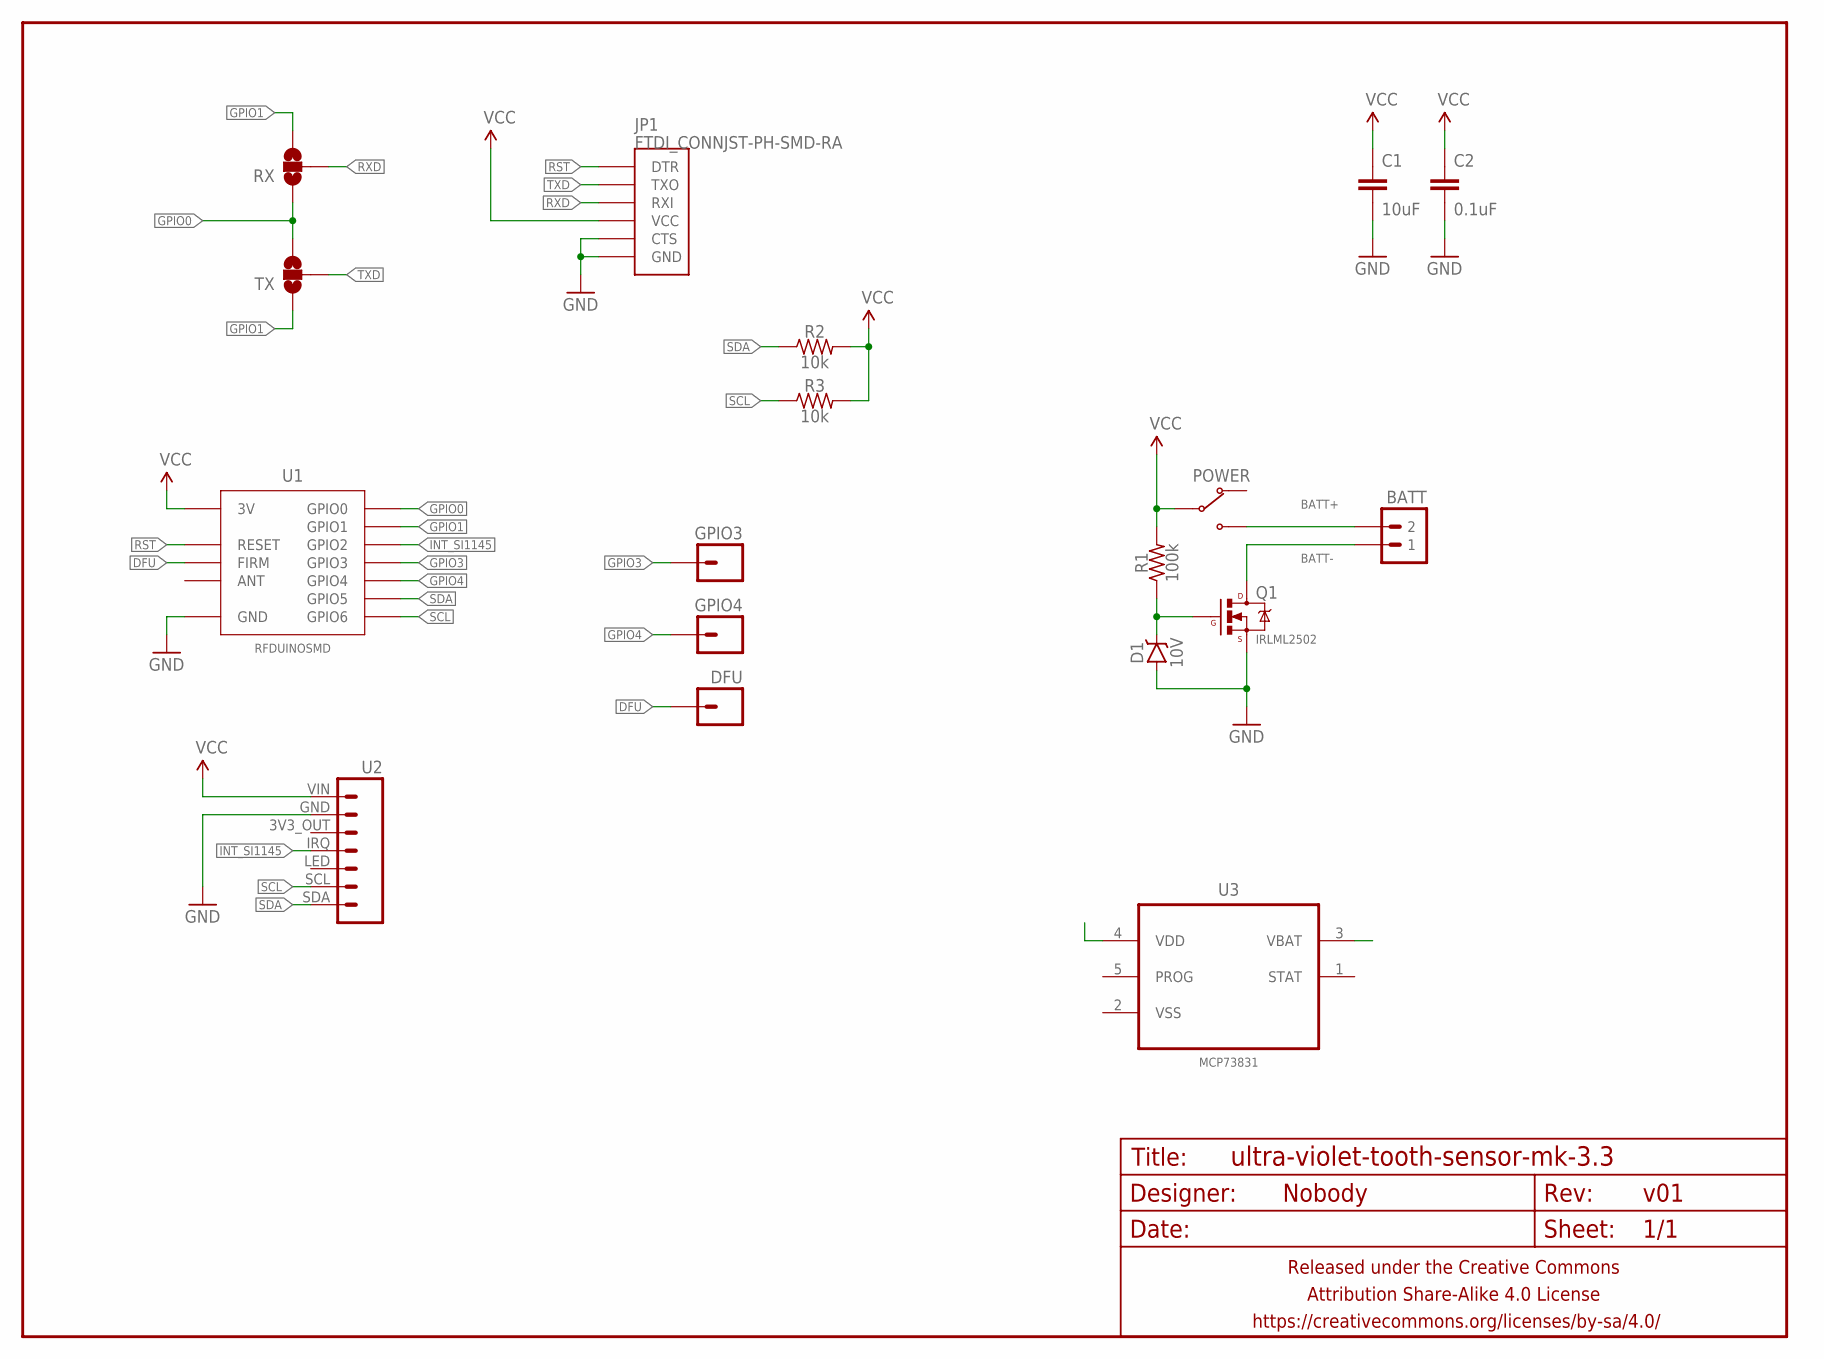
[picture p40: schematic ultra-violet-tooth-sensor-mk-3.3.sch]

Parts:
BATT: M02PTH-CENTERED-R+; 1X02-CENTER-R+
C1: 10uF; C1206
C2: 0.1uF; C0805
D1: 10V; SOT23
DFU: M01SMD_1.5X2MM; 1X01_1.5X2MM
FRAME1: FRAME-LETTERNO_PACKAGE; DUMMY
GPIO3, GPIO4: M01SMD_1.5X2MM; 1X01_1.5X2MM
JP1: FTDI_CONNJST-PH-SMD-RA; AVRISP-JST-6-PH-RA-SMD
POWER: SWITCH-SPDTPTH-RA-2.54MM; SPDT-RA-2.54MM
Q1: IRLML2502; SOT23
R1: 100k; R0805
R2, R3: 10k; R0805
RX: JUMPER-PAD-3-NOFULL_BOX_SILK; PAD-JUMPER-3-NO_YES_SILK_FULL_BOX
TX: JUMPER-PAD-3-NOFULL_BOX_SILK; PAD-JUMPER-3-NO_YES_SILK_FULL_BOX
U1: RFDUINOSMD; RFDUINO-SMD
U2: ADAFRUIT-SI1145-BREAKOUTNOHOLEY; ADAFRUIT-SI1145-BREAKOUT-NOHOLES
U3: MCP73831; SOT95P280X145-5N

Connections:
BATT+: BATT.2, POWER.3 (NO)
BATT-: BATT.1, Q1.3 (D)
DFU: DFU.P$1, U1.FACTORY (FIRM)
GND: C1.2, C2.2, D1.1 (A), D1.2 (A), JP1.CTS, JP1.GND, Q1.2 (S), U1.GND@1 (GND), U1.GND@2 (GND), U1.GND@3 (GND), U1.GND@4 (GND), U1.GND@5 (GND), U1.GND@6 (GND), U1.GND@7 (GND), U1.GND@8 (GND), U2.GND
GPIO0: RX.1, TX.3, U1.GPIO0
GPIO1: RX.3, TX.1, U1.GPIO1
GPIO3: GPIO3.P$1, U1.GPIO3
GPIO4: GPIO4.P$1, U1.GPIO4
INT_SI1145: U1.GPIO2, U2.IRQ
unnamed: D1.3 (C), Q1.1 (G), R1.1
RST: JP1.DTR, U1.RESET
RXD: JP1.RXI, RX.2
SCL: R3.1, U1.GPIO6, U2.SCL
SDA: R2.1, U1.GPIO5, U2.SDA
TXD: JP1.TXO, TX.2
VCC: C1.1, C2.1, JP1.VCC, POWER.2 (COM), R1.2, R2.2, R3.2, U1.3V, U2.VIN
VSS: U3.2 (VSS)

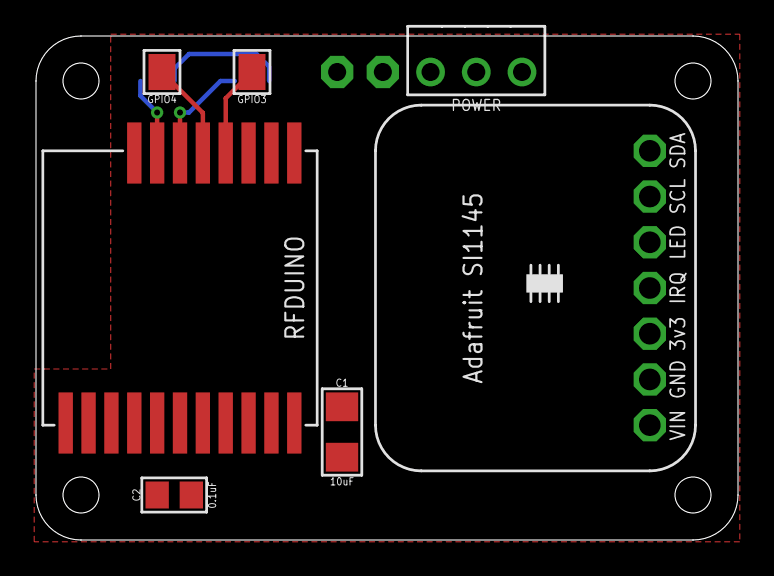
[picture p41: board ultra-violet-tooth-sensor-mk-3.3.brd from above]

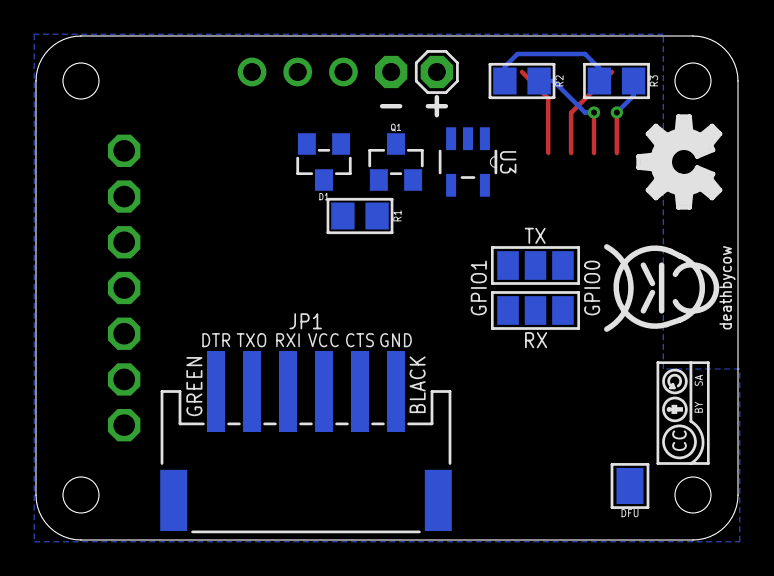
[picture p42: board ultra-violet-tooth-sensor-mk-3.3.brd from below]

Board: 2 copper layers, 39.0 x 28.0 mm, 22 parts (14 on the bottom side), 16 nets.

Other parts of the board:
U$1: CC-BY-SA-4.0-NO-URL
U$2: COW_SMALL
U$6: OSHWLOGO_SILKONLY
