schizobovine/uvdosimeter/hardware/ultra-violet-tooth-sensor-mk-2.4.brd

## EAGLE design hardware/ultra-violet-tooth-sensor-mk-2.4.brd (2015-06-01)

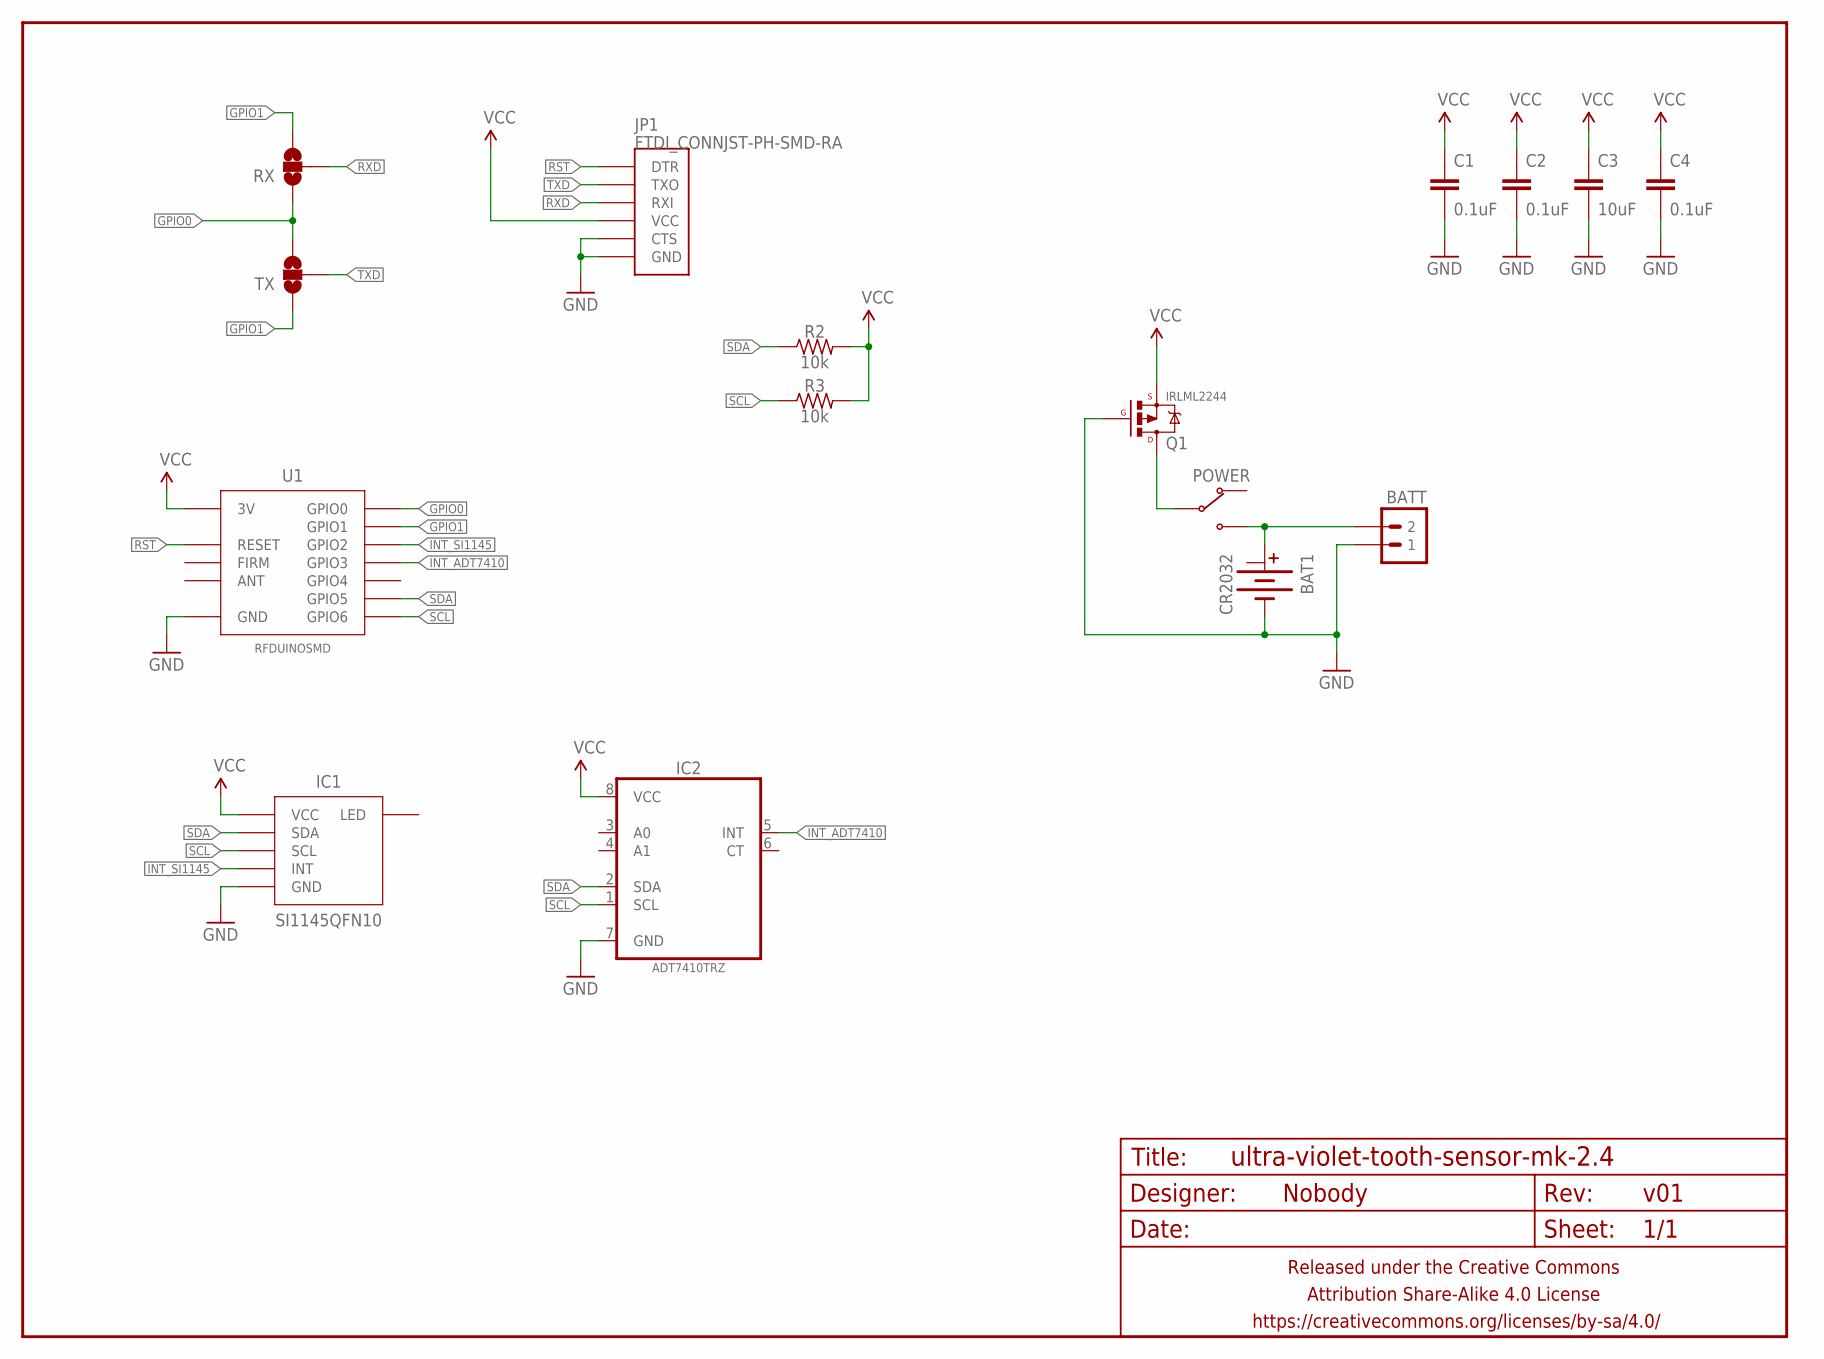
[picture p43: schematic ultra-violet-tooth-sensor-mk-2.4.sch]

Parts:
BAT1: CR2032; BATTCON_20MM_MINE_STAHPIT
BATT: M02PTH-CENTERED-R+; 1X02-CENTER-R+
C1: 0.1uF; C0805
C2, C4: 0.1uF; C0603
C3: 10uF; C1206
FRAME1: FRAME-LETTERNO_PACKAGE; DUMMY
IC1: SI1145QFN10; SI1145
IC2: ADT7410TRZ; SOIC127P600X175-8N
JP1: FTDI_CONNJST-PH-SMD-RA; AVRISP-JST-6-PH-RA-SMD
POWER: SWITCH-SPDTPTH-RA-2.54MM; SPDT-RA-2.54MM
Q1: IRLML2244; SOT23-3
R2, R3: 10k; R0603
RX: JUMPER-PAD-3-NOFULL_BOX_SILK; PAD-JUMPER-3-NO_YES_SILK_FULL_BOX
TX: JUMPER-PAD-3-NOFULL_BOX_SILK; PAD-JUMPER-3-NO_YES_SILK_FULL_BOX
U1: RFDUINOSMD; RFDUINO-SMD

Connections:
GND: BAT1.BOTTOM (-), BATT.1, C1.2, C2.2, C3.2, C4.2, IC1.GND, IC2.7 (GND), JP1.CTS, JP1.GND, Q1.1 (G), U1.GND@1 (GND), U1.GND@2 (GND), U1.GND@3 (GND), U1.GND@4 (GND), U1.GND@5 (GND), U1.GND@6 (GND), U1.GND@7 (GND), U1.GND@8 (GND)
GPIO0: RX.1, TX.3, U1.GPIO0
GPIO1: RX.3, TX.1, U1.GPIO1
INT_ADT7410: IC2.5 (INT), U1.GPIO3
INT_SI1145: IC1.INT, U1.GPIO2
unnamed: BAT1.TOP@1 (+), BATT.2, POWER.3 (NO)
unnamed: POWER.2 (COM), Q1.3 (D)
RST: JP1.DTR, U1.RESET
RXD: JP1.RXI, RX.2
SCL: IC1.SCL, IC2.1 (SCL), R3.1, U1.GPIO6
SDA: IC1.SDA, IC2.2 (SDA), R2.1, U1.GPIO5
TXD: JP1.TXO, TX.2
VCC: C1.1, C2.1, C3.1, C4.1, IC1.VCC@1 (VCC), IC1.VCC@2 (VCC), IC1.VCC@3 (VCC), IC2.8 (VCC), JP1.VCC, Q1.2 (S), R2.2, R3.2, U1.3V

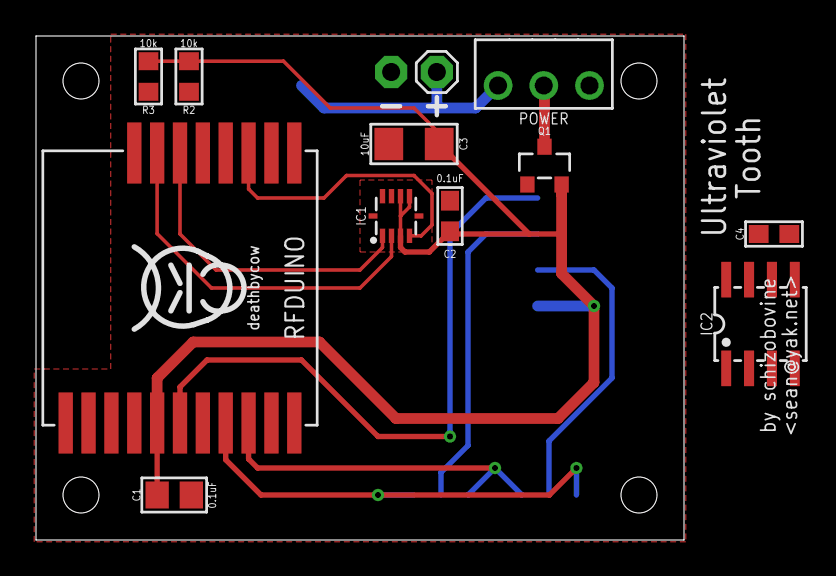
[picture p44: board ultra-violet-tooth-sensor-mk-2.4.brd from above]

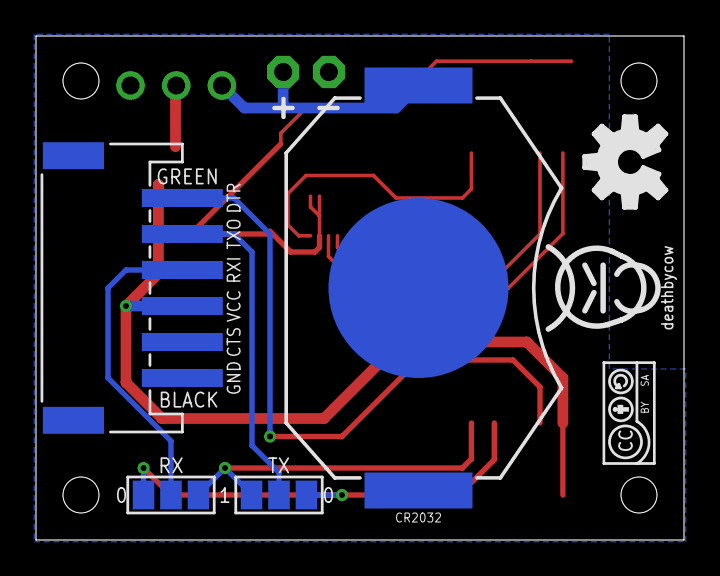
[picture p45: board ultra-violet-tooth-sensor-mk-2.4.brd from below]

Board: 2 copper layers, 36.0 x 28.0 mm, 21 parts (7 on the bottom side), 13 nets.

Other parts of the board:
U$1: CC-BY-SA-4.0-NO-URL
U$2, U$5: COW_SMALL
U$6: OSHWLOGO_SILKONLY
