schizobovine/uvdosimeter/hardware/ultra-violet-tooth-sensor-mk-2.0.brd

## EAGLE design hardware/ultra-violet-tooth-sensor-mk-2.0.brd (2015-05-18)

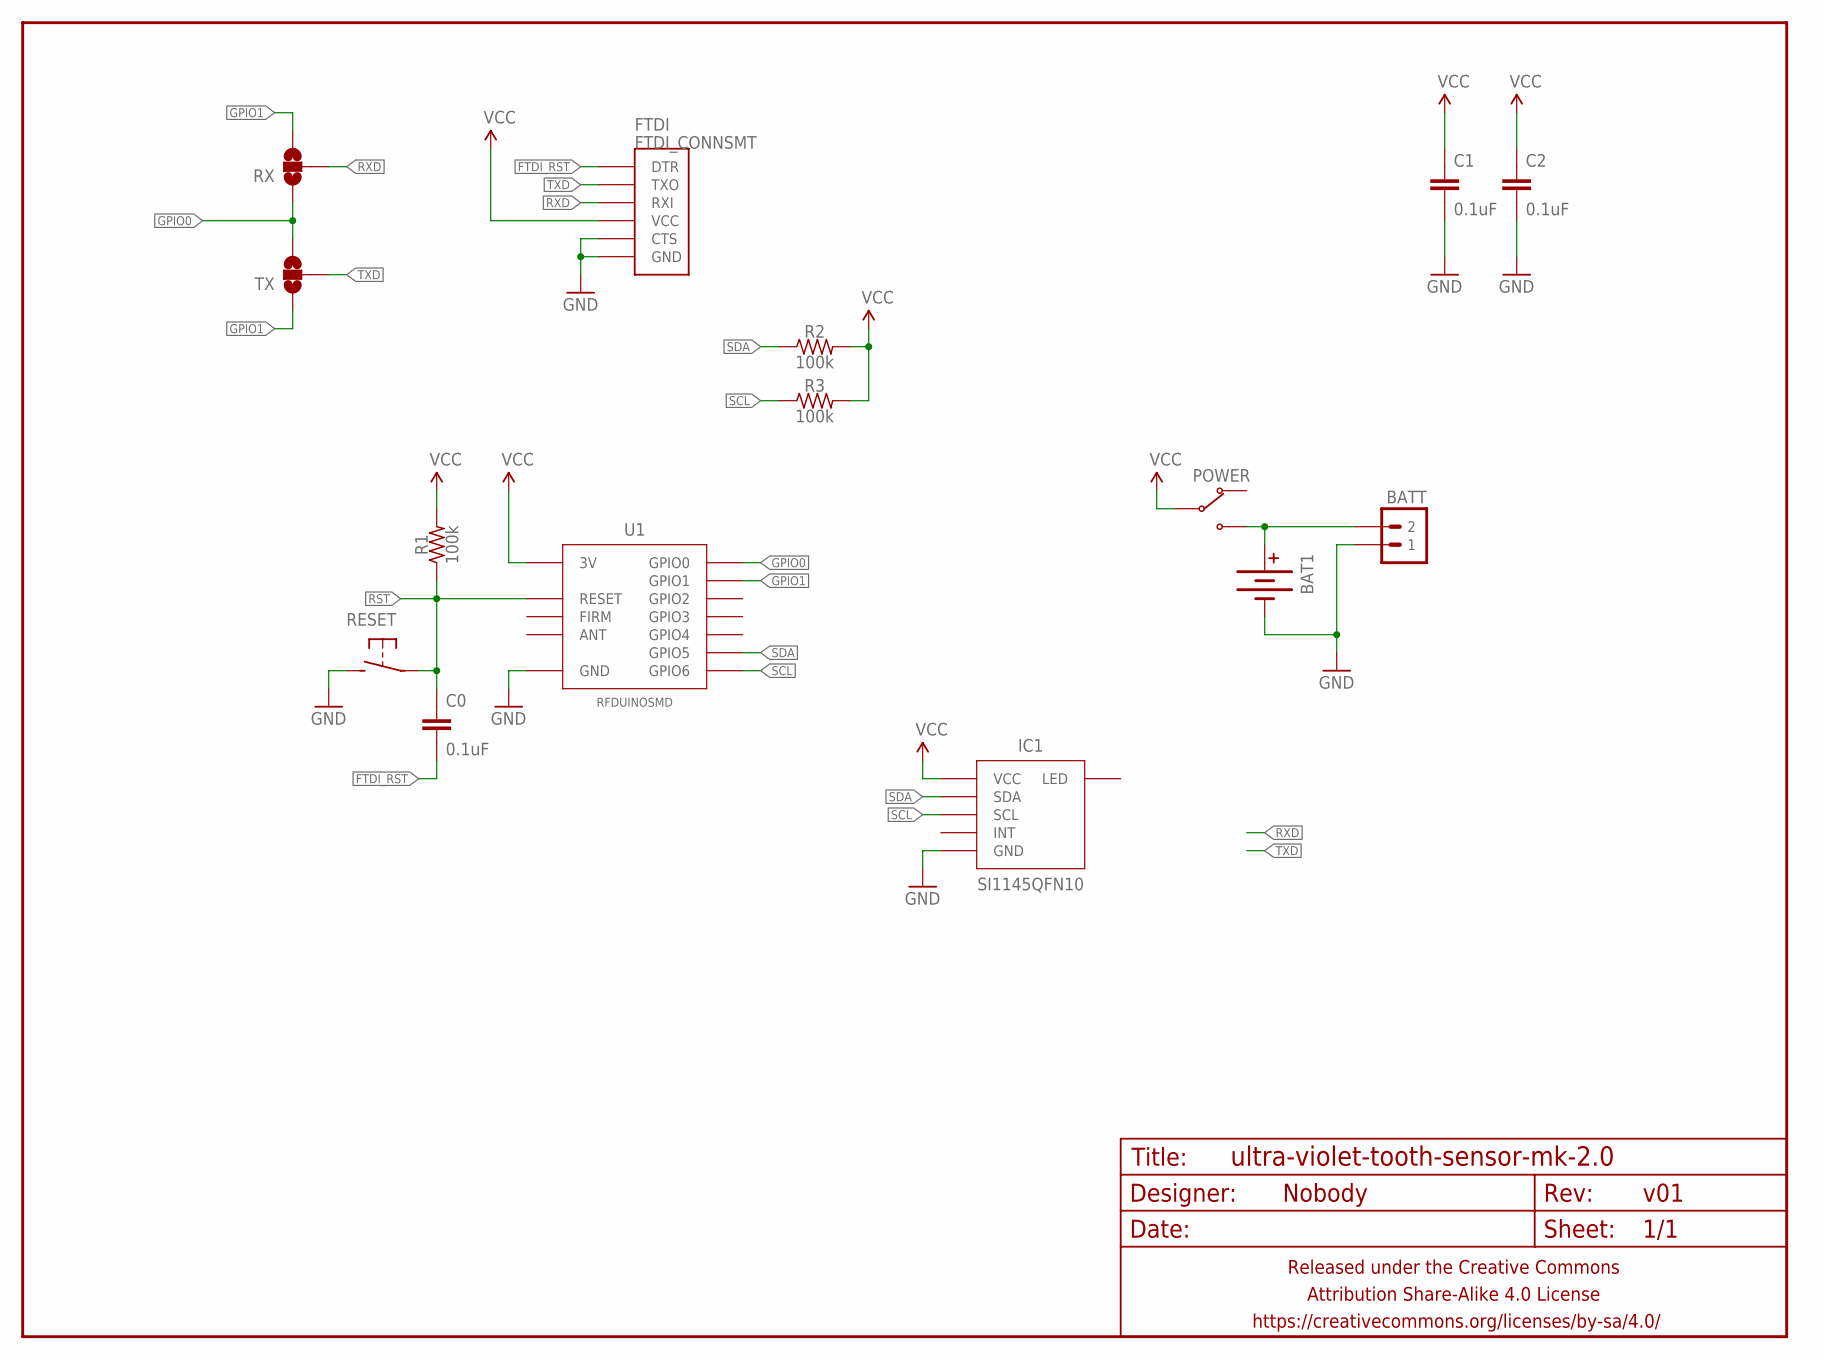
[picture p46: schematic ultra-violet-tooth-sensor-mk-2.0.sch]

Parts:
BAT1: BATTERY20MMSMD-MINE; BATTCON_20MM_MINE
BATT: M02PTH-CENTERED-R+; 1X02-CENTER-R+
C0, C1, C2: 0.1uF; C0805
FRAME1: FRAME-LETTERNO_PACKAGE; DUMMY
FTDI: FTDI_CONNSMT; FTDI_CONN_SMT
IC1: SI1145QFN10; SI1145
POWER: SWITCH-SPDTSMD-RA; SWITCH-SPDT-SMD-RA
R1, R2, R3: 100k; R0805
RESET: SPST-NO-TACTSMD-TINY; TACTILE-SWITCH-SMD
RX: JUMPER-PAD-3-NOFULL_BOX_SILK; PAD-JUMPER-3-NO_YES_SILK_FULL_BOX
TX: JUMPER-PAD-3-NOFULL_BOX_SILK; PAD-JUMPER-3-NO_YES_SILK_FULL_BOX
U1: RFDUINOSMD; RFDUINO-SMD

Connections:
FTDI_RST: C0.2, FTDI.DTR
GND: BAT1.BOTTOM (-), BATT.1, C1.2, C2.2, FTDI.CTS, FTDI.GND, IC1.GND, RESET.B@1 (2), RESET.B@2 (2), U1.GND@1 (GND), U1.GND@2 (GND), U1.GND@3 (GND), U1.GND@4 (GND), U1.GND@5 (GND), U1.GND@6 (GND), U1.GND@7 (GND), U1.GND@8 (GND)
GPIO0: RX.1, TX.3, U1.GPIO0
GPIO1: RX.3, TX.1, U1.GPIO1
unnamed: BAT1.TOP@1 (+), BAT1.TOP@2 (+), BATT.2, POWER.1 (NO)
RST: C0.1, R1.1, RESET.A@1 (1), RESET.A@2 (1), U1.RESET
RXD: FTDI.RXI, RX.2
SCL: IC1.SCL, R3.1, U1.GPIO6
SDA: IC1.SDA, R2.1, U1.GPIO5
TXD: FTDI.TXO, TX.2
VCC: C1.1, C2.1, FTDI.VCC, IC1.VCC@1 (VCC), IC1.VCC@2 (VCC), IC1.VCC@3 (VCC), POWER.2 (COM), R1.2, R2.2, R3.2, U1.3V

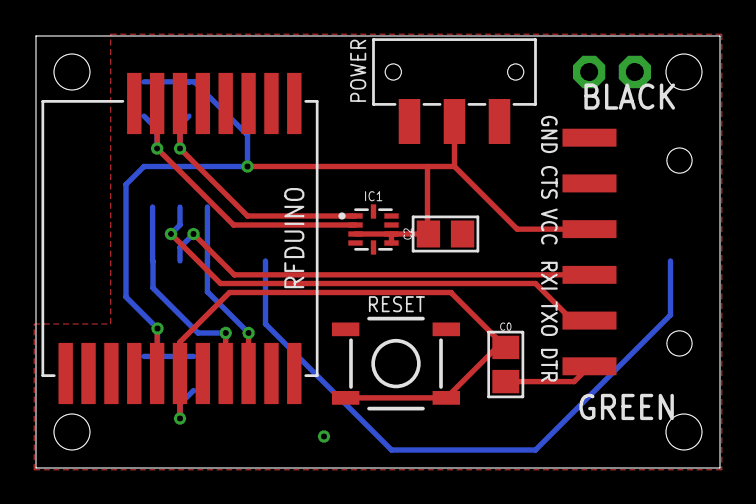
[picture p47: board ultra-violet-tooth-sensor-mk-2.0.brd from above]

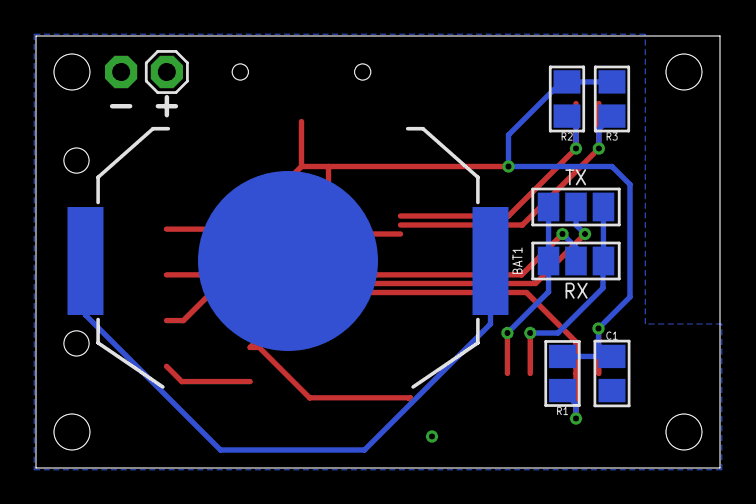
[picture p48: board ultra-violet-tooth-sensor-mk-2.0.brd from below]

Board: 2 copper layers, 38.0 x 24.0 mm, 19 parts (8 on the bottom side), 11 nets.

Other parts of the board:
U$1: CC-BY-SA-4.0-NO-URL
U$3: OSHWLOGO_TOP_0.2
U$4: COW_SMALL_METAL
