schizobovine/uvdosimeter/hardware/ultra-violet-tooth-sensor-mk-1.0.brd

## EAGLE design hardware/ultra-violet-tooth-sensor-mk-1.0.brd (2015-05-18)

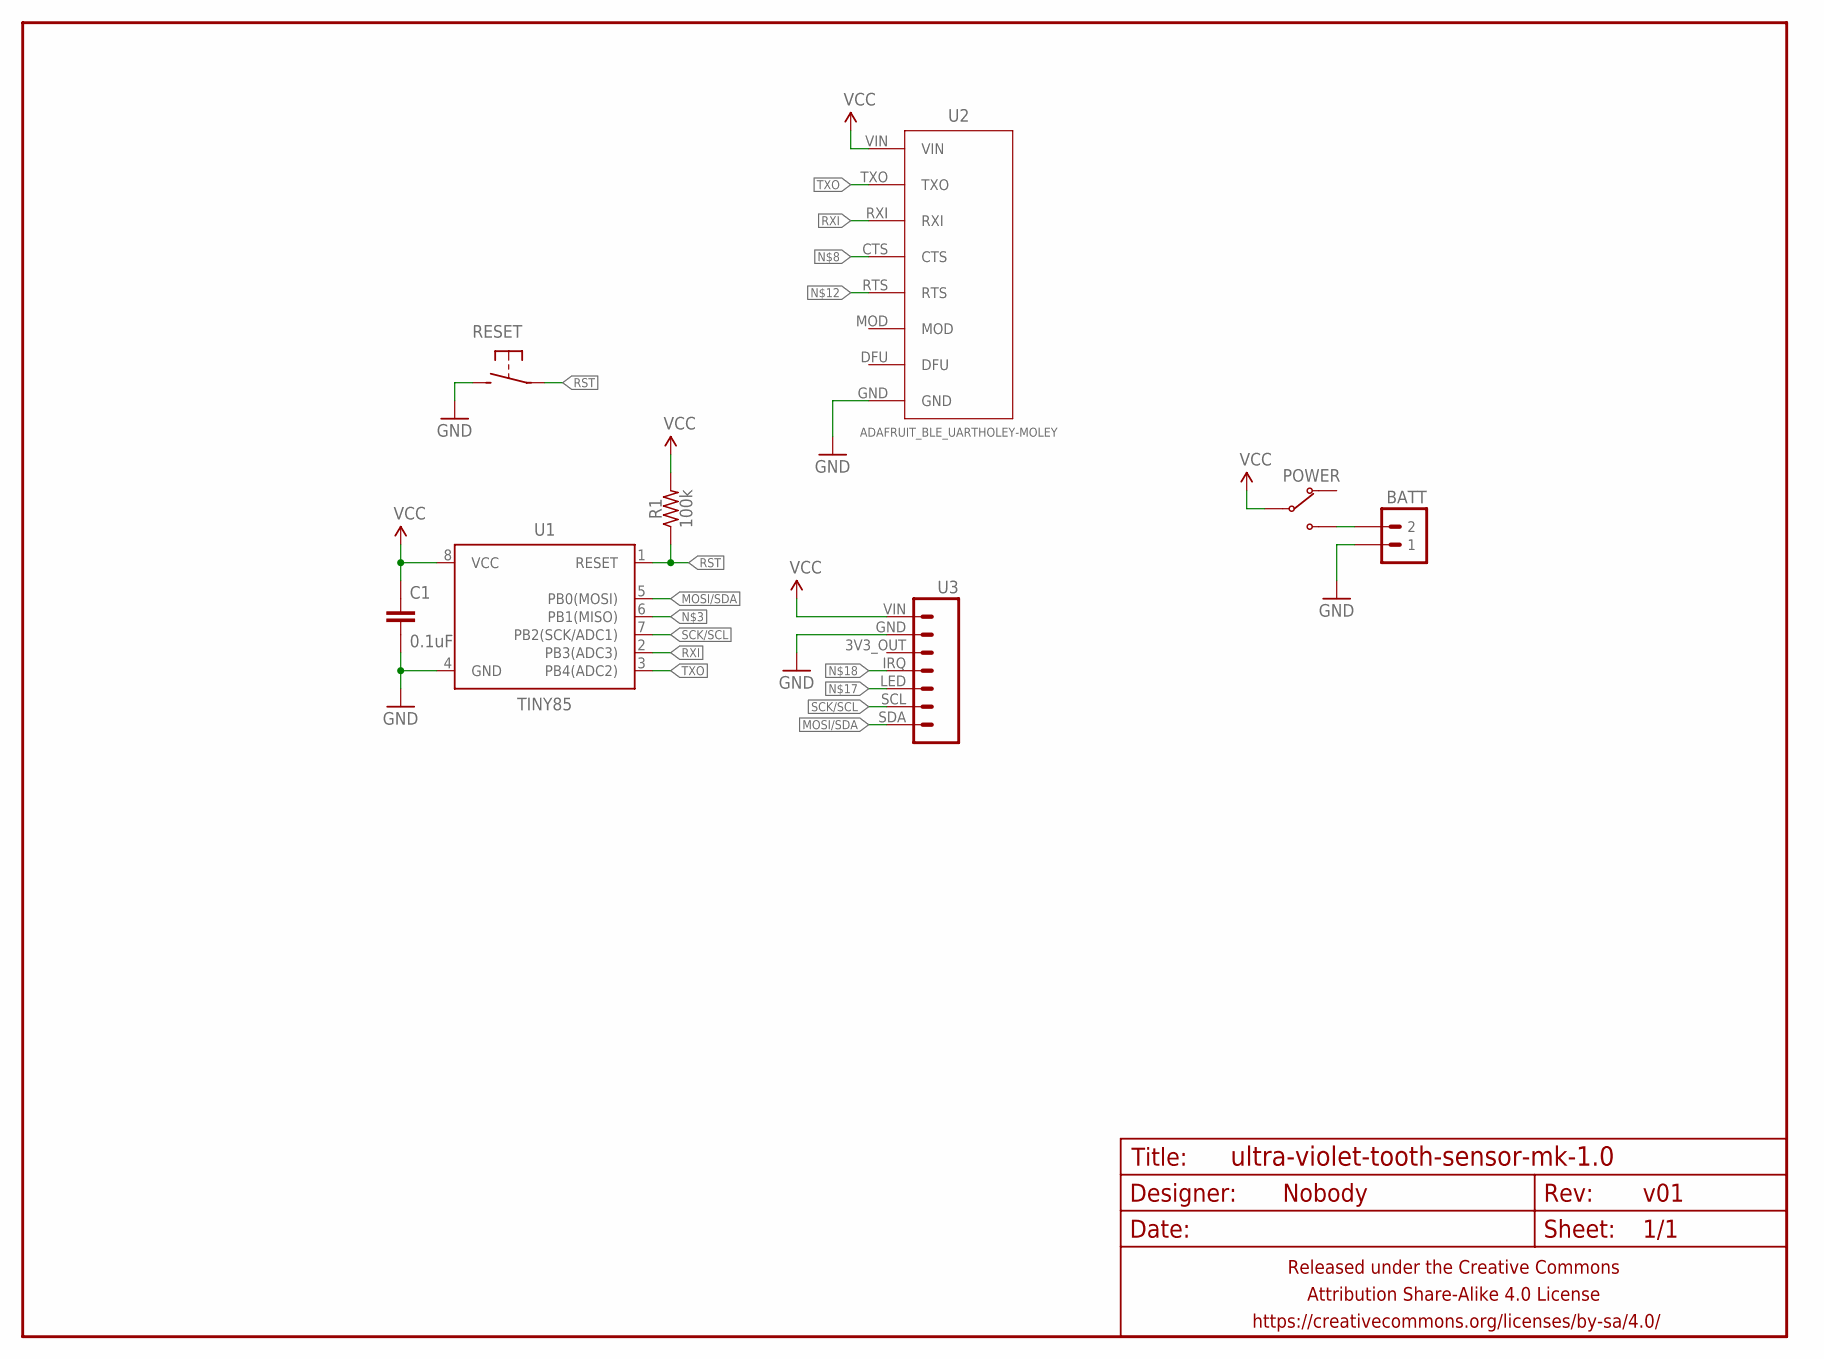
[picture p52: schematic ultra-violet-tooth-sensor-mk-1.0.sch]

Parts:
BATT: M02PTH-CENTERED-R+; 1X02-CENTER-R+
C1: 0.1uF; C025-024X044
FRAME1: FRAME-LETTERNO_PACKAGE; DUMMY
POWER: SWITCH-SPDTPTH-RA-2.54MM; SPDT-RA-2.54MM
R1: 100k; RESISTOR-AXIAL-PTH-7.62MM
RESET: SPST-NO-TACT3MM-RA; TACTILE-PTH-SIDE
U1: TINY85; DIP08
U2: ADAFRUIT_BLE_UARTHOLEY-MOLEY; ADAFRUIT_BLE_UART_HOLEY
U3: ADAFRUIT-SI1145-BREAKOUT

Connections:
GND: BATT.1, C1.2, RESET.2, U1.4 (GND), U2.GND, U3.GND
MOSI/SDA: U1.5 (PB0(MOSI)), U3.SDA
unnamed: BATT.2, POWER.3 (NO)
RST: R1.P$1 (1), RESET.1, U1.1 (RESET)
RXI: U1.2 (PB3(ADC3)), U2.RXI
SCK/SCL: U1.7 (PB2(SCK/ADC1)), U3.SCL
TXO: U1.3 (PB4(ADC2)), U2.TXO
VCC: C1.1, POWER.2 (COM), R1.P$2 (2), U1.8 (VCC), U2.VIN, U3.VIN

Board: 2 copper layers, 9 parts (2 on the bottom side), 8 nets, no tracks yet.
