schizobovine/uvdosimeter/hardware/ultra-violet-tooth-sensor-mk-3.0.brd

## EAGLE design hardware/ultra-violet-tooth-sensor-mk-3.0.brd (2015-05-18)

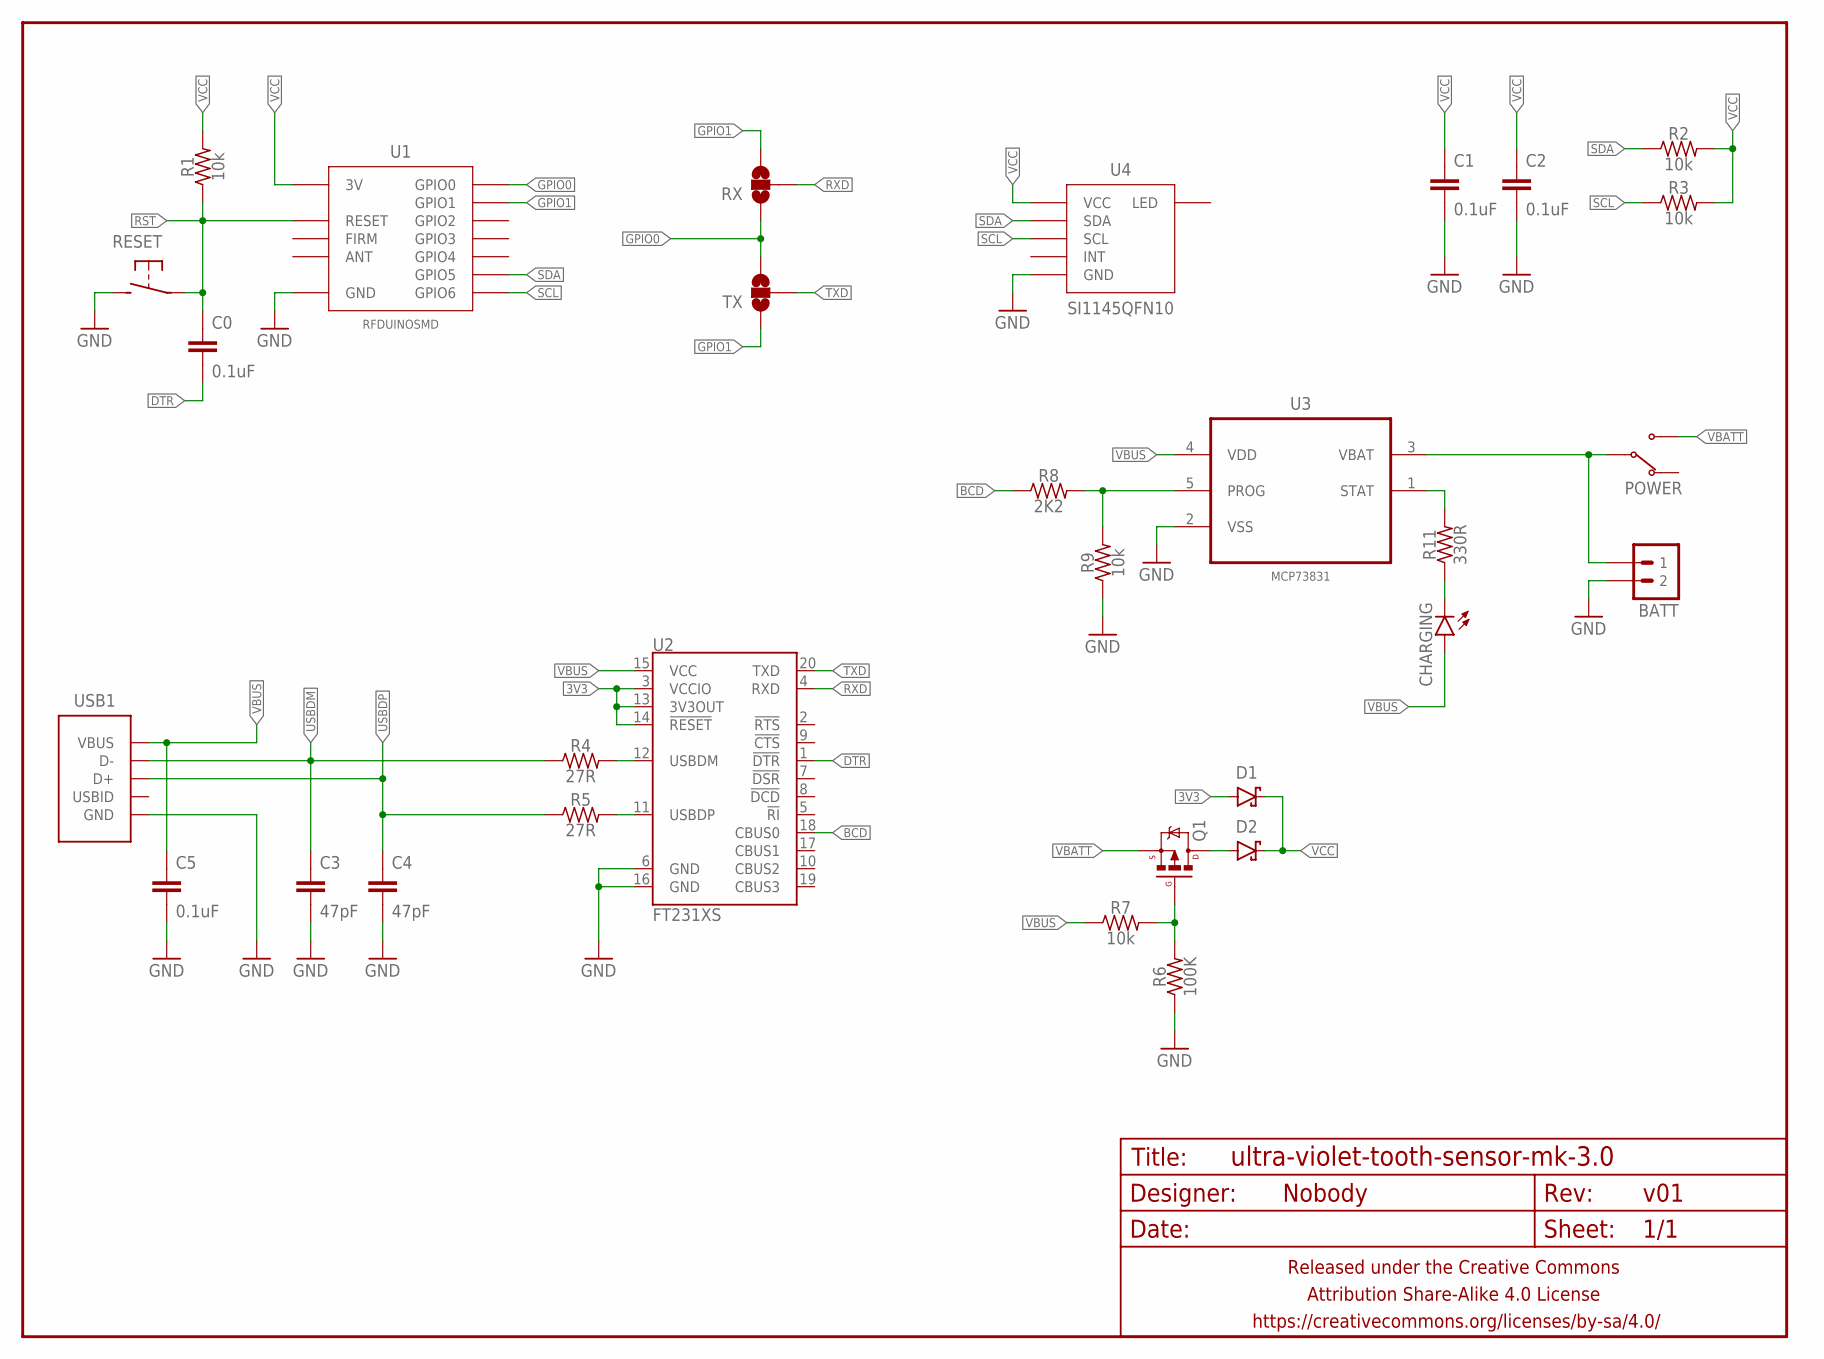
[picture p56: schematic ultra-violet-tooth-sensor-mk-3.0.sch]

Parts:
BATT: M02JST-2MM-SMT; JST-2-SMD
C0, C1, C2, C5: 0.1uF; C0603
C3, C4: 47pF; C0603
CHARGING: LED1206; LED-1206
D1, D2: DIODE-SCHOTTKYSMA; SMA-DIODE-SCHOTTKY
FRAME1: FRAME-LETTERNO_PACKAGE; DUMMY
POWER: SWITCH-SPDTPTH-RA-2.54MM; SPDT-RA-2.54MM
Q1: MOSFET-PCHANNELIRLML2244; SOT23-3
R1, R2, R3, R7, R9: 10k; R0603
R4, R5: 27R; R0603
R6: 100K; R0603
R8: 2K2; R0603
R11: 330R; R0603
RESET: SPST-NO-TACT3MM-RA; TACTILE-PTH-SIDE
RX: JUMPER-PAD-3-NOFULL_BOX_SILK; PAD-JUMPER-3-NO_YES_SILK_FULL_BOX
TX: JUMPER-PAD-3-NOFULL_BOX_SILK; PAD-JUMPER-3-NO_YES_SILK_FULL_BOX
U1: RFDUINOSMD; RFDUINO-SMD
U2: FT231XS; SSOP20_L
U3: MCP73831; SOT95P280X145-5N
U4: SI1145QFN10; SI1145
USB1: USB-ABCOMBO; USB-MICRO-B-FCI-CUTOUT

Connections:
3V3: D1.A, U2.3 (VCCIO), U2.13 (3V3OUT), U2.14 (!RESET)
BCD: R8.1, U2.18 (CBUS0)
DTR: C0.2, U2.1 (!DTR)
GND: BATT.1 (2), C1.2, C2.2, C3.2, C4.2, C5.2, R6.1, R9.1, RESET.2, U1.GND@1 (GND), U1.GND@2 (GND), U1.GND@3 (GND), U1.GND@4 (GND), U1.GND@5 (GND), U1.GND@6 (GND), U1.GND@7 (GND), U1.GND@8 (GND), U2.6 (GND), U2.16 (GND), U3.2 (VSS), U4.GND, USB1.5 (GND), USB1.P$1 (GND), USB1.P$2 (GND)
GPIO0: RX.1, TX.3, U1.GPIO0
GPIO1: RX.3, TX.1, U1.GPIO1
unnamed: Q1.1 (G), R6.2, R7.2
unnamed: BATT.2 (1), POWER.2 (COM), U3.3 (VBAT)
unnamed: R11.2, U3.1 (STAT)
unnamed: CHARGING.C, R11.1
unnamed: D2.A, Q1.3 (D)
unnamed: R4.2, U2.12 (USBDM)
unnamed: R5.2, U2.11 (USBDP)
PROG: R8.2, R9.2, U3.5 (PROG)
RST: C0.1, R1.1, RESET.1, U1.RESET
RXD: RX.2, U2.4 (RXD)
SCL: R3.1, U1.GPIO6, U4.SCL
SDA: R2.1, U1.GPIO5, U4.SDA
TXD: TX.2, U2.20 (TXD)
USBDM: C3.1, R4.1, USB1.2 (D-)
USBDP: C4.1, R5.1, USB1.3 (D+)
VBATT: POWER.3 (NO), Q1.2 (S)
VBUS: C5.1, CHARGING.A, R7.1, U2.15 (VCC), U3.4 (VDD), USB1.1 (VBUS)
VCC: C1.1, C2.1, D1.C, D2.C, R1.2, R2.2, R3.2, U1.3V, U4.VCC@1 (VCC), U4.VCC@2 (VCC), U4.VCC@3 (VCC)

Board: 2 copper layers, 33 parts (11 on the bottom side), 24 nets, no tracks yet.

Other parts of the board:
U$1: CC-BY-SA-4.0-NO-URL
U$3: OSHWLOGO_TOP_0.2
